dushyantyadav0303/Ruby-Home-Automation/Render/ruby-render/0003.png

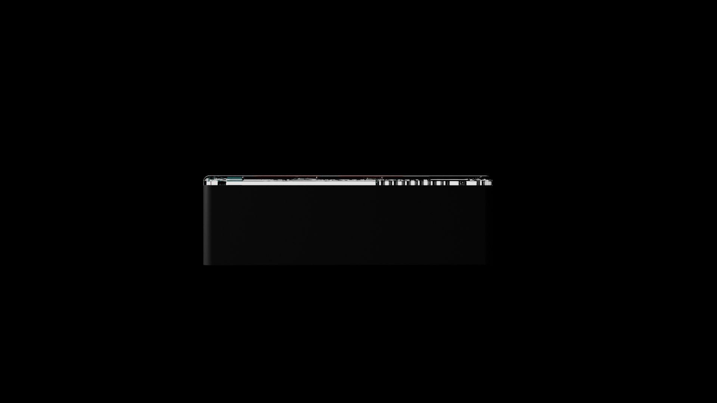
Render/ruby-render/0003.png
