dushyantyadav0303/Ruby-Home-Automation/Render/ruby-render/0030.png

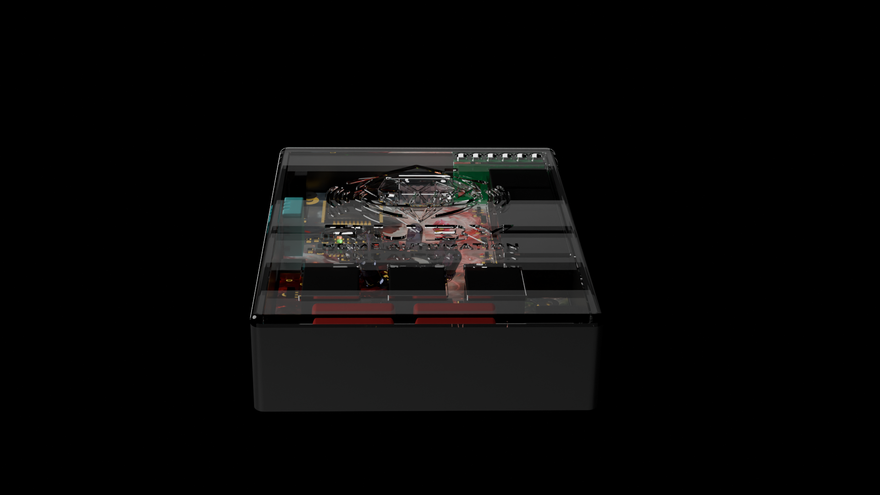
Render/ruby-render/0030.png
