dushyantyadav0303/Ruby-Home-Automation/Render/ruby-render/0039.png

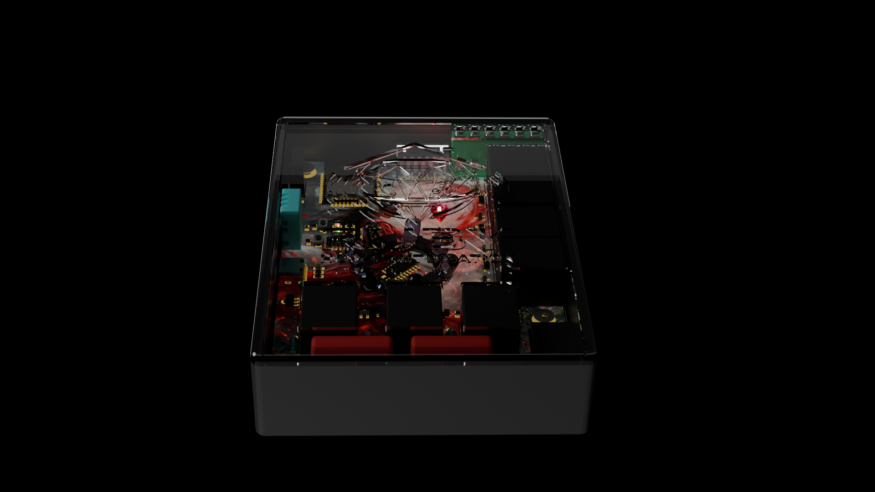
Render/ruby-render/0039.png
