dushyantyadav0303/Ruby-Home-Automation/Render/ruby-render/0087.png

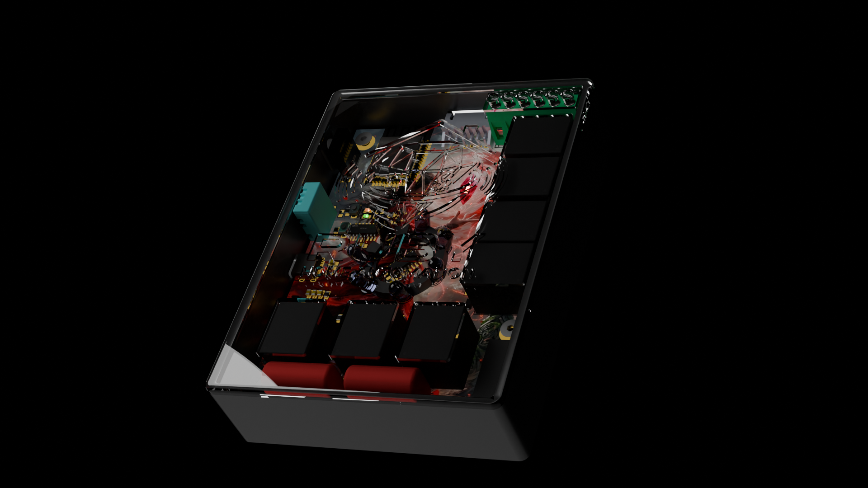
Render/ruby-render/0087.png
