dushyantyadav0303/Ruby-Home-Automation/Render/ruby-render/0092.png

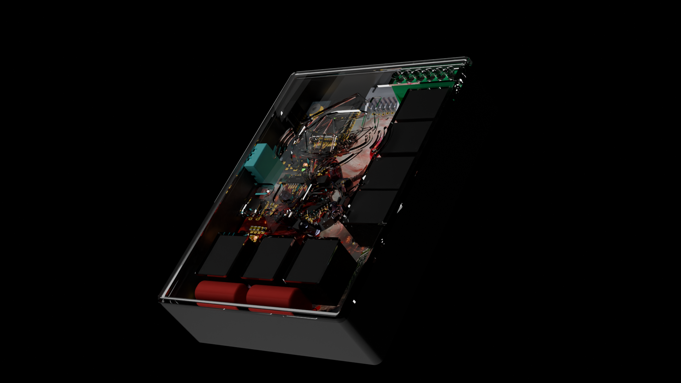
Render/ruby-render/0092.png
