dushyantyadav0303/Ruby-Home-Automation/Render/ruby-render/0105.png

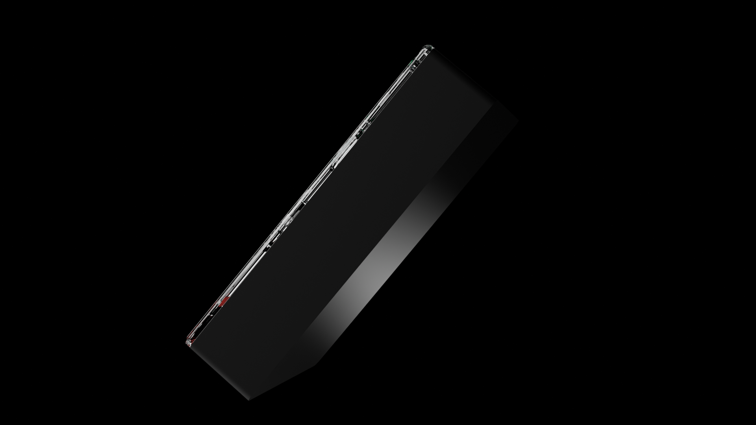
Render/ruby-render/0105.png
