dushyantyadav0303/Ruby-Home-Automation/Render/ruby-render/0107.png

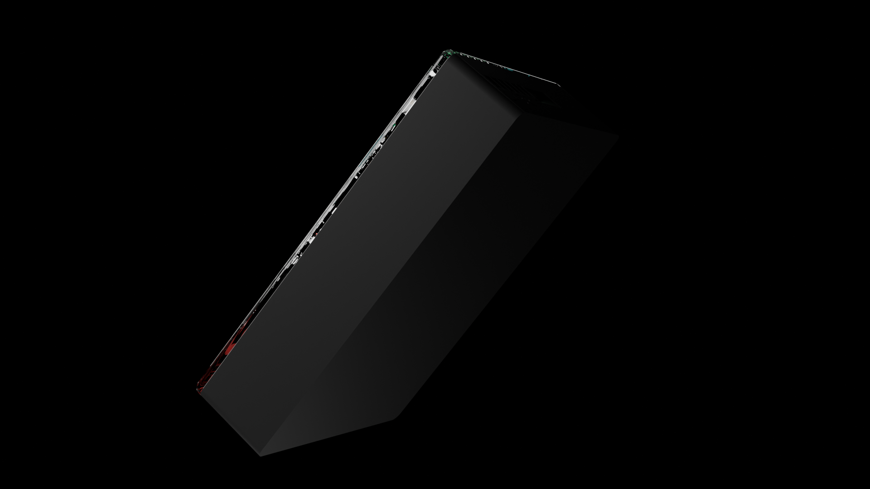
Render/ruby-render/0107.png
