dushyantyadav0303/Ruby-Home-Automation/Render/ruby-render/0113.png

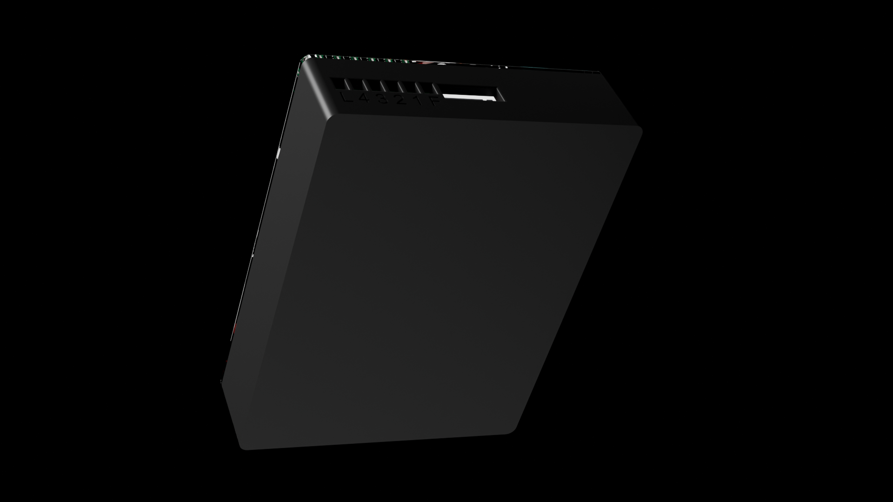
Render/ruby-render/0113.png
