dushyantyadav0303/Ruby-Home-Automation/Render/ruby-render/0117.png

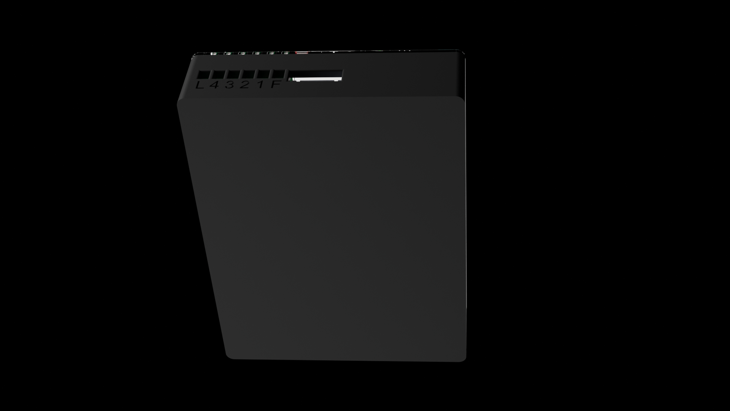
Render/ruby-render/0117.png
