dushyantyadav0303/Ruby-Home-Automation/Render/ruby-render/0119.png

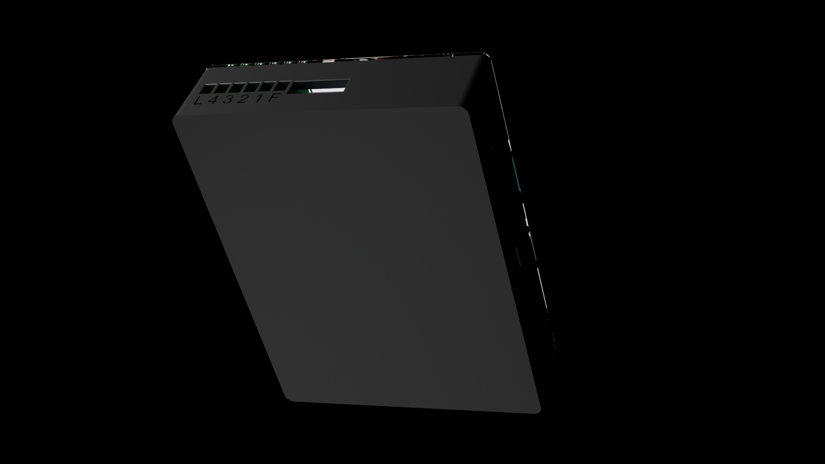
Render/ruby-render/0119.png
