dushyantyadav0303/Ruby-Home-Automation/Render/ruby-render/0123.png

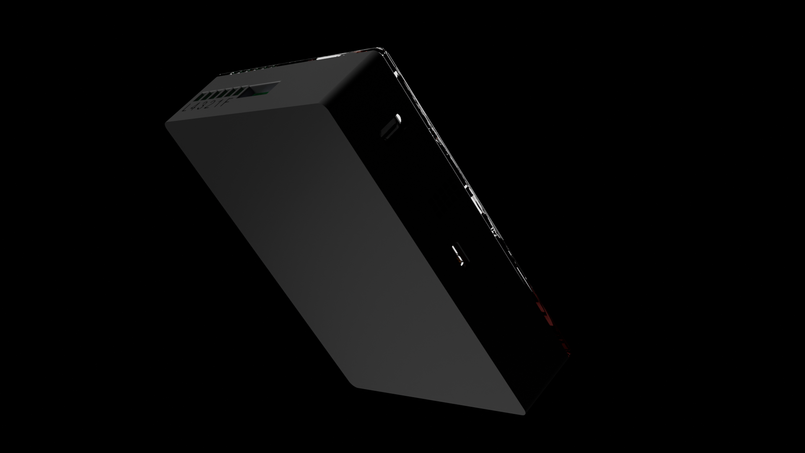
Render/ruby-render/0123.png
