dushyantyadav0303/Ruby-Home-Automation/Render/ruby-render/0125.png

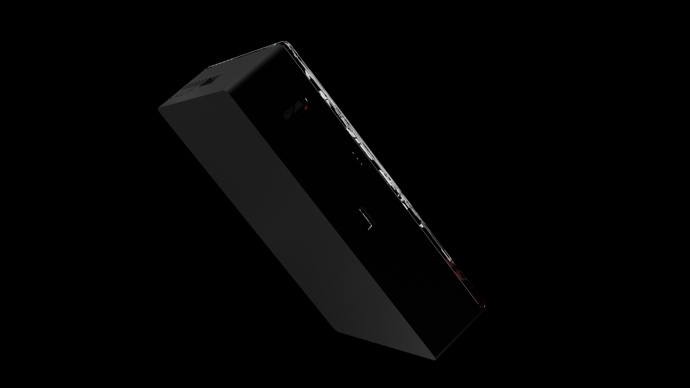
Render/ruby-render/0125.png
