dushyantyadav0303/Ruby-Home-Automation/Render/ruby-render/0128.png

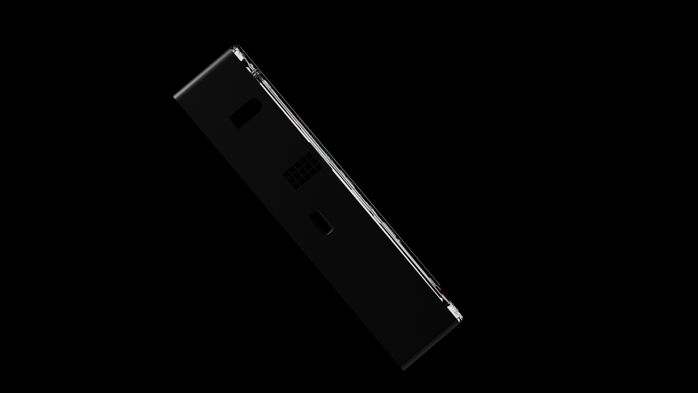
Render/ruby-render/0128.png
