dushyantyadav0303/Ruby-Home-Automation/Render/ruby-render/0132.png

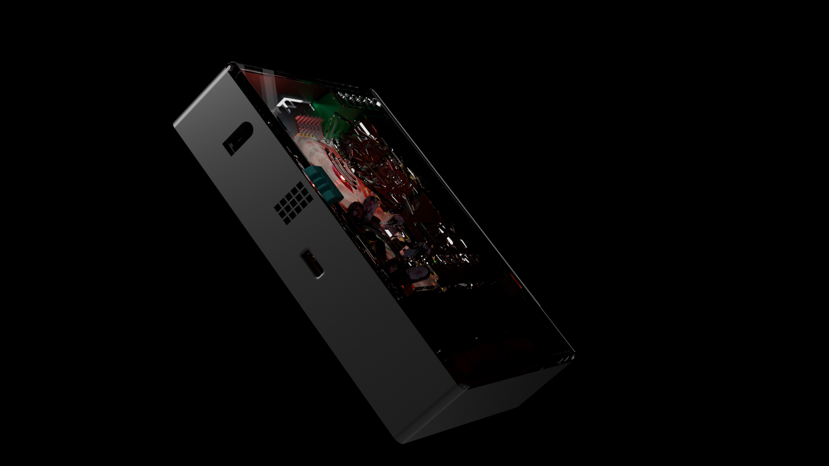
Render/ruby-render/0132.png
