dushyantyadav0303/Ruby-Home-Automation/Render/ruby-render/0135.png

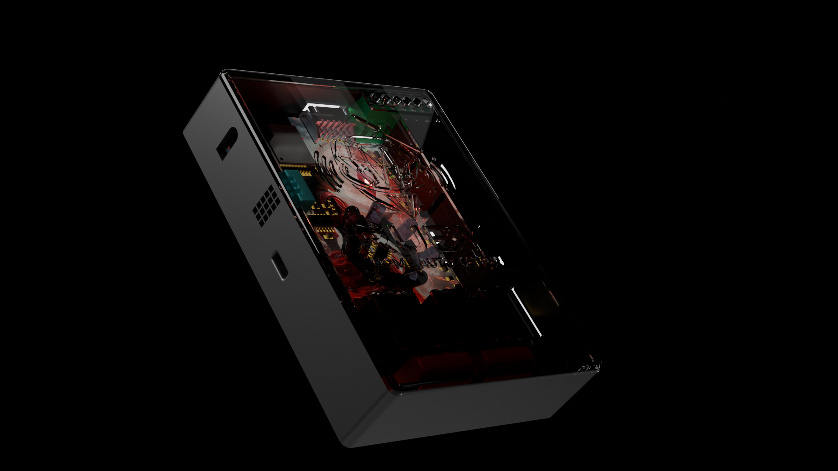
Render/ruby-render/0135.png
