dushyantyadav0303/Ruby-Home-Automation/Render/ruby-render/0141.png

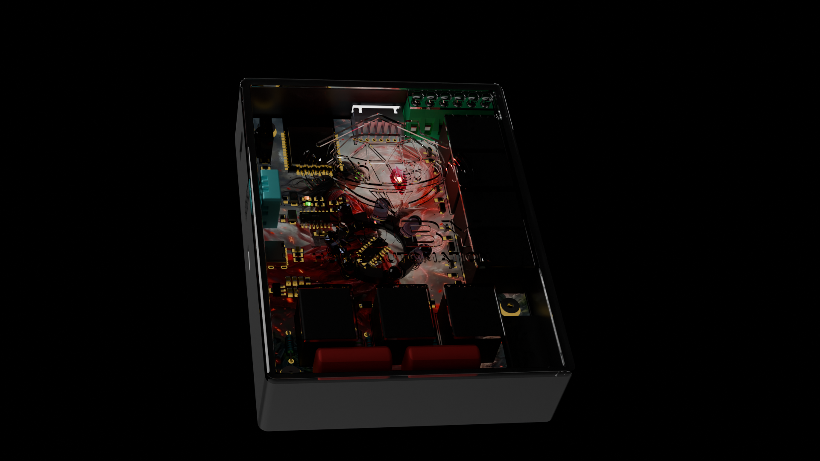
Render/ruby-render/0141.png
