dushyantyadav0303/Ruby-Home-Automation/Render/ruby-render/0150.png

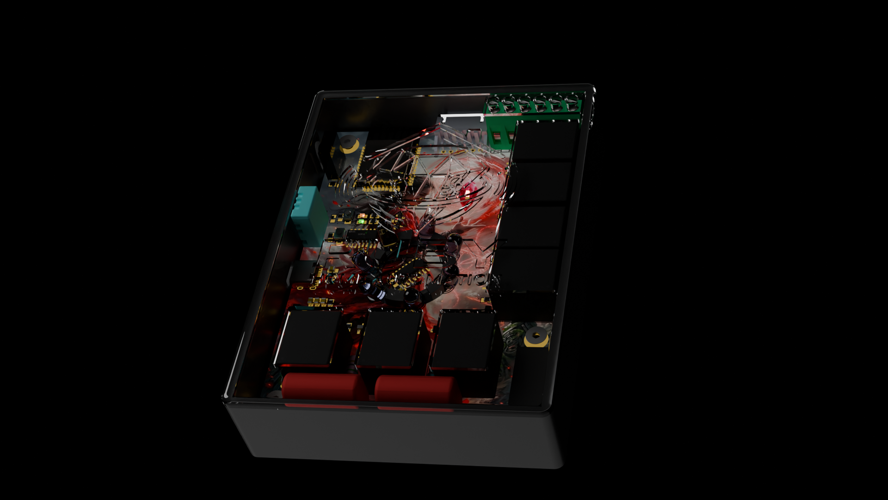
Render/ruby-render/0150.png
