dushyantyadav0303/Ruby-Home-Automation/Render/ruby-render/0172.png

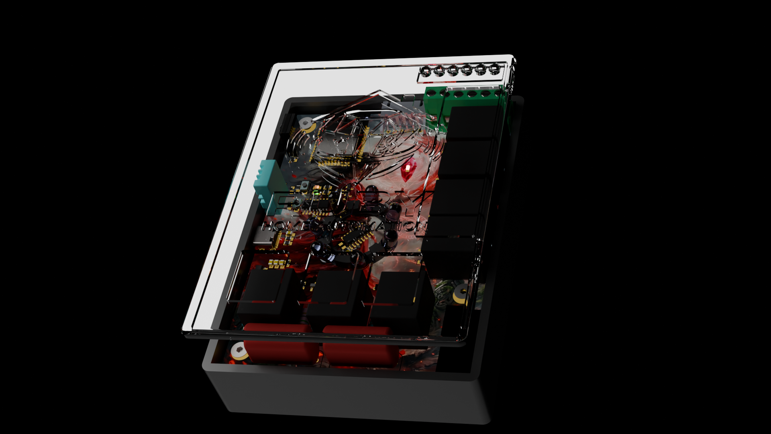
Render/ruby-render/0172.png
