dushyantyadav0303/Ruby-Home-Automation/Render/ruby-render/0174.png

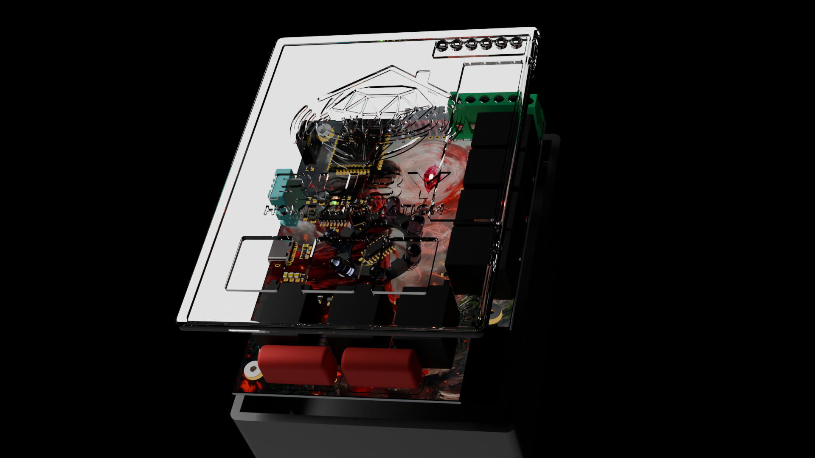
Render/ruby-render/0174.png
