dushyantyadav0303/Ruby-Home-Automation/Render/ruby-render/0175.png

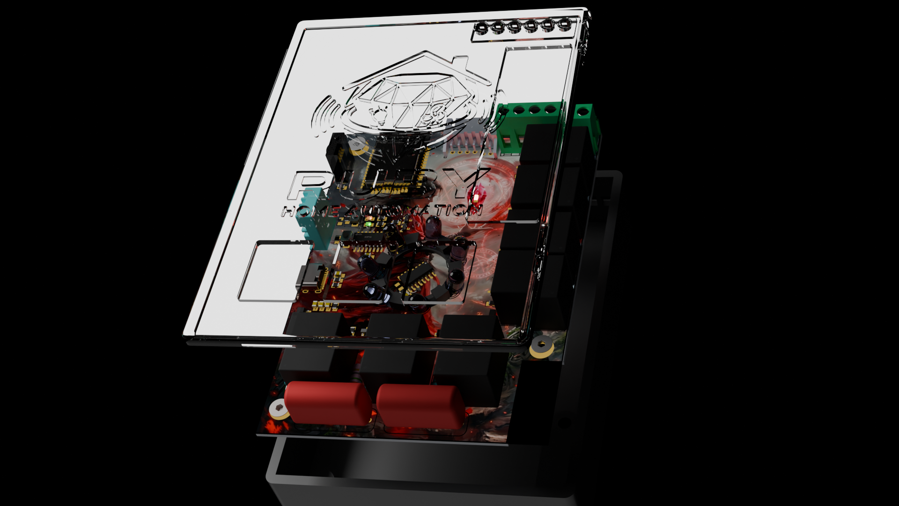
Render/ruby-render/0175.png
