dushyantyadav0303/Ruby-Home-Automation/Render/ruby-render/0176.png

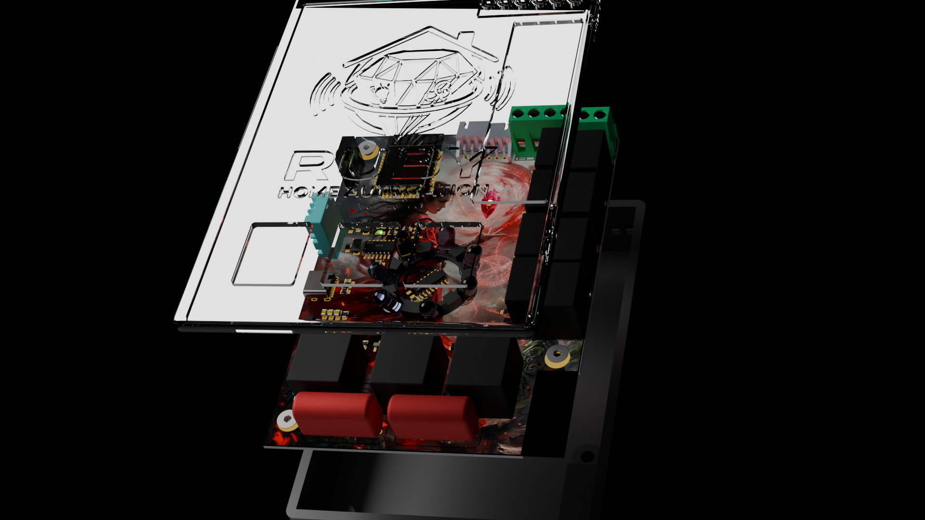
Render/ruby-render/0176.png
