dushyantyadav0303/Ruby-Home-Automation/Render/ruby-render/0179.png

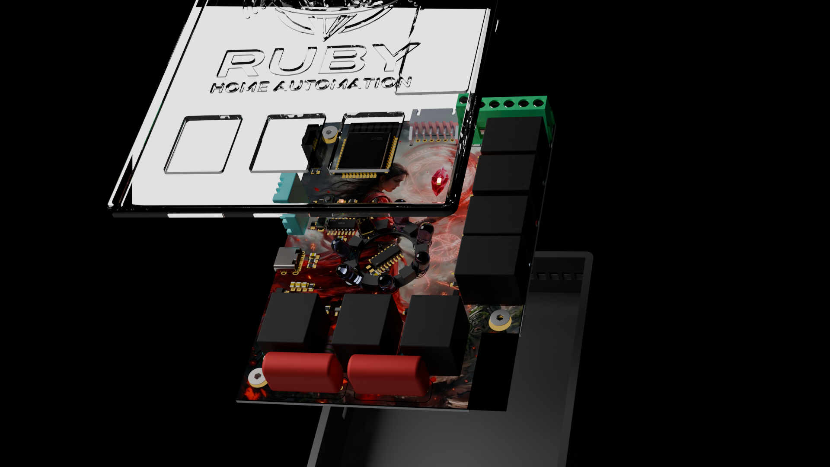
Render/ruby-render/0179.png
