dushyantyadav0303/Ruby-Home-Automation/Render/ruby-render/0182.png

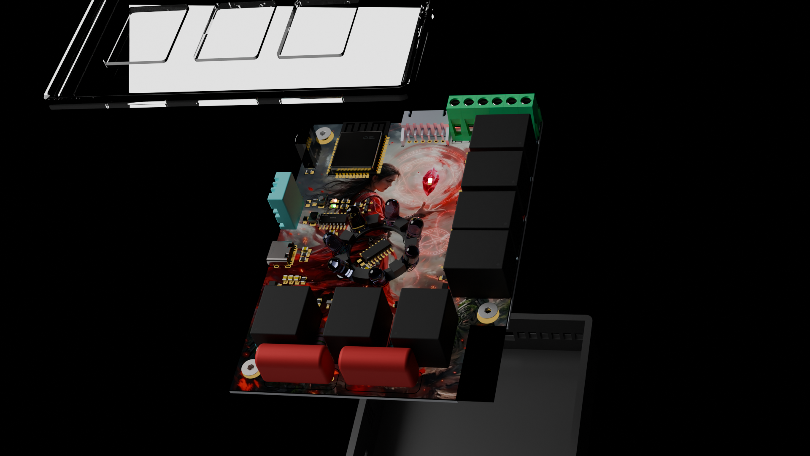
Render/ruby-render/0182.png
