dushyantyadav0303/Ruby-Home-Automation/Render/ruby-render/0186.png

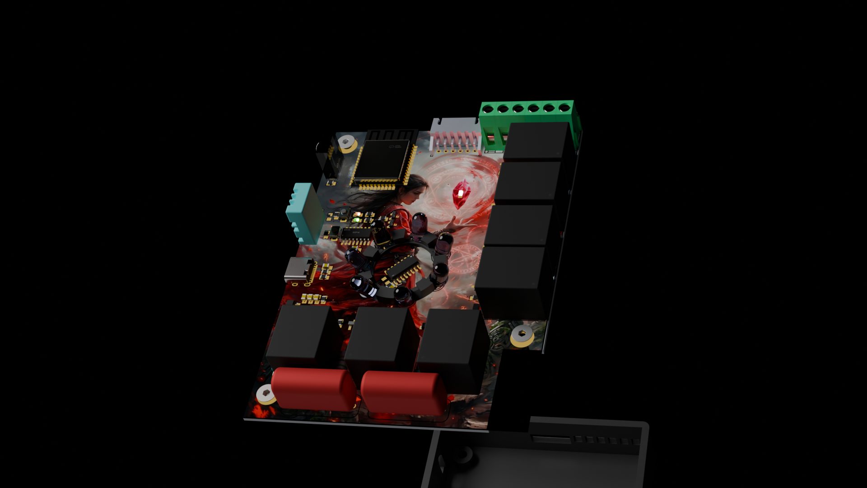
Render/ruby-render/0186.png
