dushyantyadav0303/Ruby-Home-Automation/Render/ruby-render/0207.png

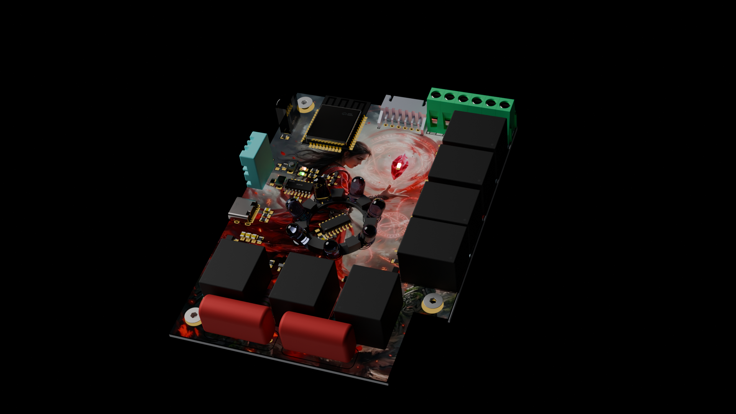
Render/ruby-render/0207.png
