dushyantyadav0303/Ruby-Home-Automation/Render/ruby-render/0215.png

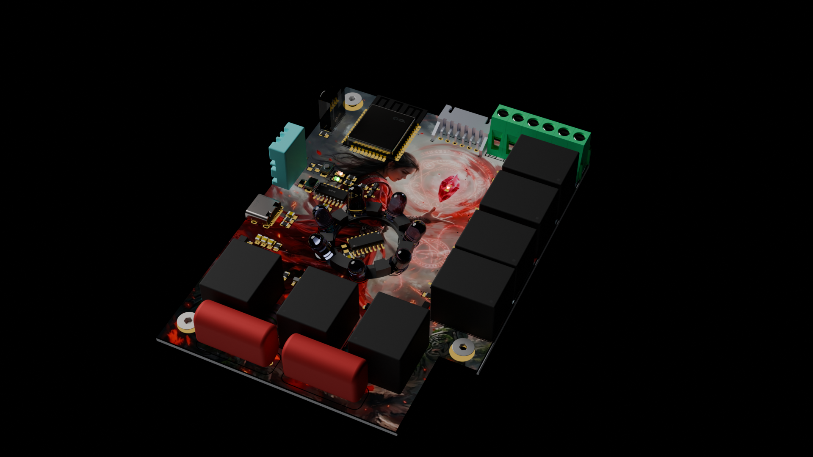
Render/ruby-render/0215.png
