dushyantyadav0303/Ruby-Home-Automation/Render/ruby-render/0223.png

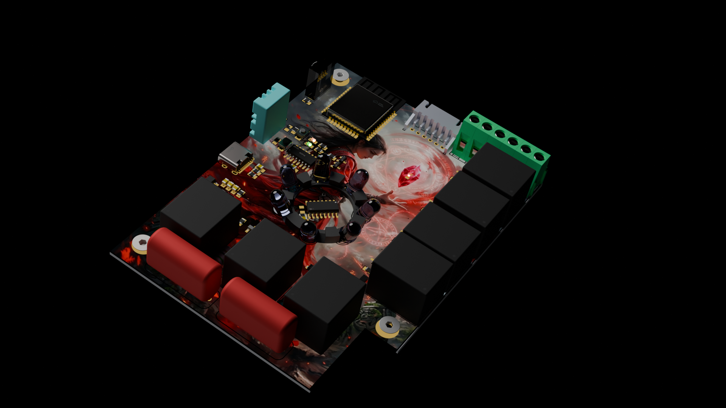
Render/ruby-render/0223.png
