dushyantyadav0303/Ruby-Home-Automation/Render/ruby-render/0230.png

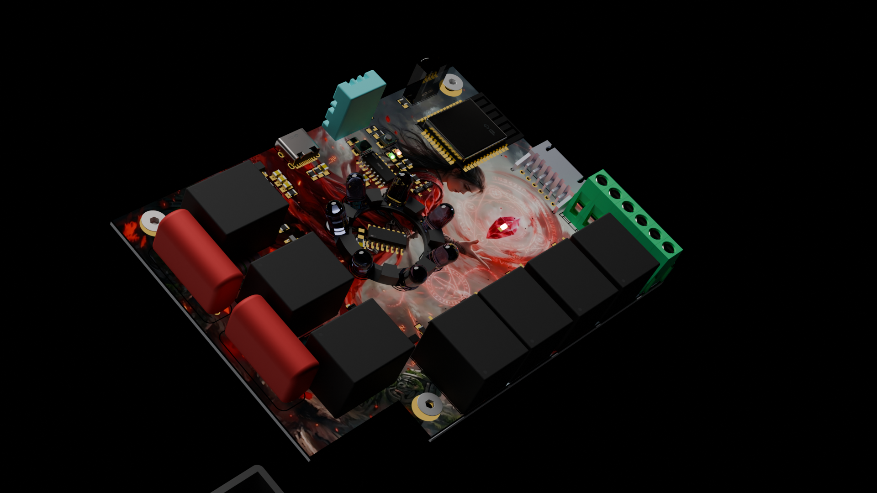
Render/ruby-render/0230.png
