dushyantyadav0303/Ruby-Home-Automation/Render/ruby-render/0233.png

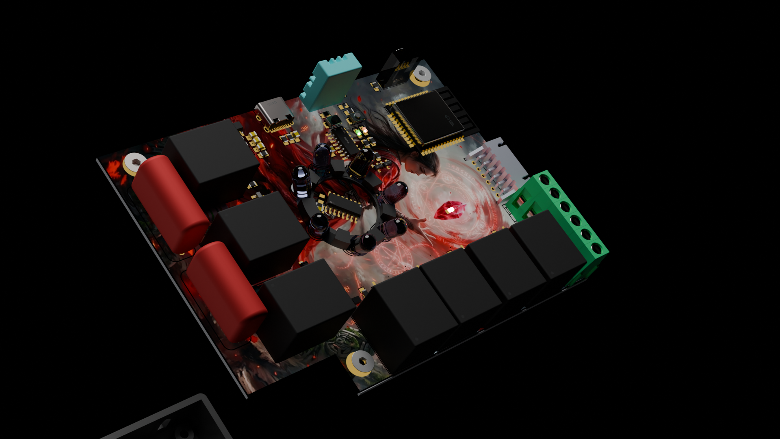
Render/ruby-render/0233.png
