dushyantyadav0303/Ruby-Home-Automation/Render/ruby-render/0237.png

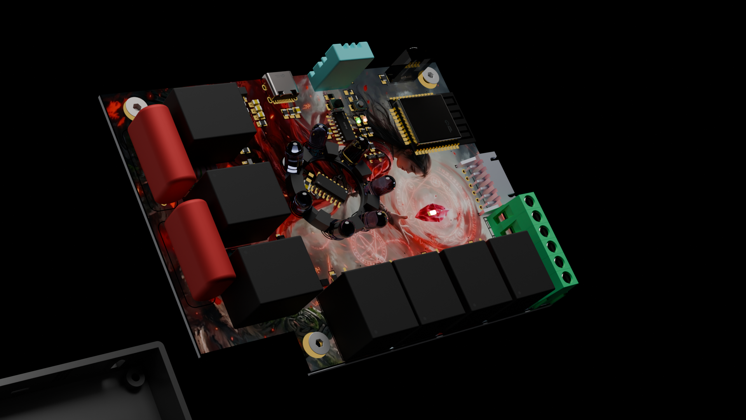
Render/ruby-render/0237.png
