dushyantyadav0303/Ruby-Home-Automation/Render/ruby-render/0243.png

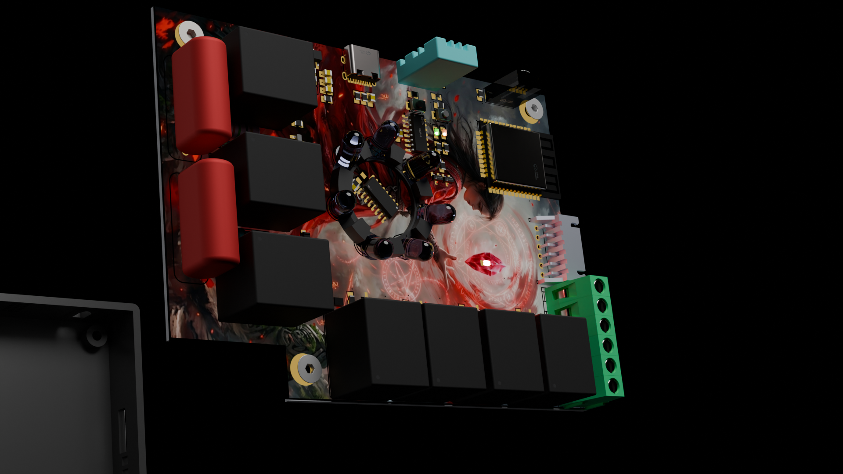
Render/ruby-render/0243.png
