dushyantyadav0303/Ruby-Home-Automation/Render/ruby-render/0248.png

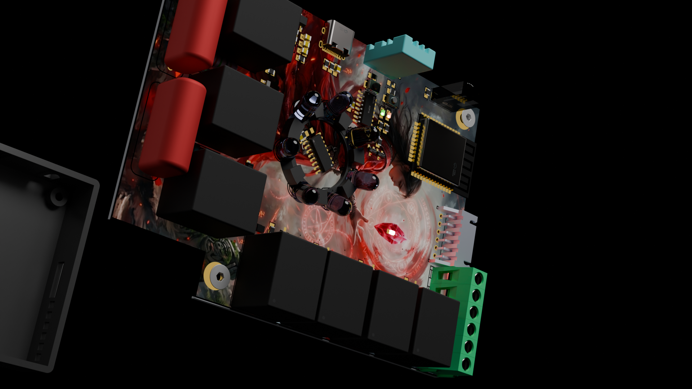
Render/ruby-render/0248.png
