dushyantyadav0303/Ruby-Home-Automation/Render/ruby-render/0249.png

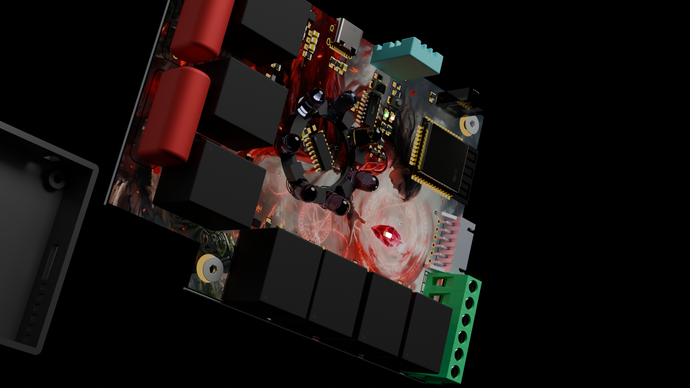
Render/ruby-render/0249.png
