dushyantyadav0303/Ruby-Home-Automation/Render/ruby-render/0250.png

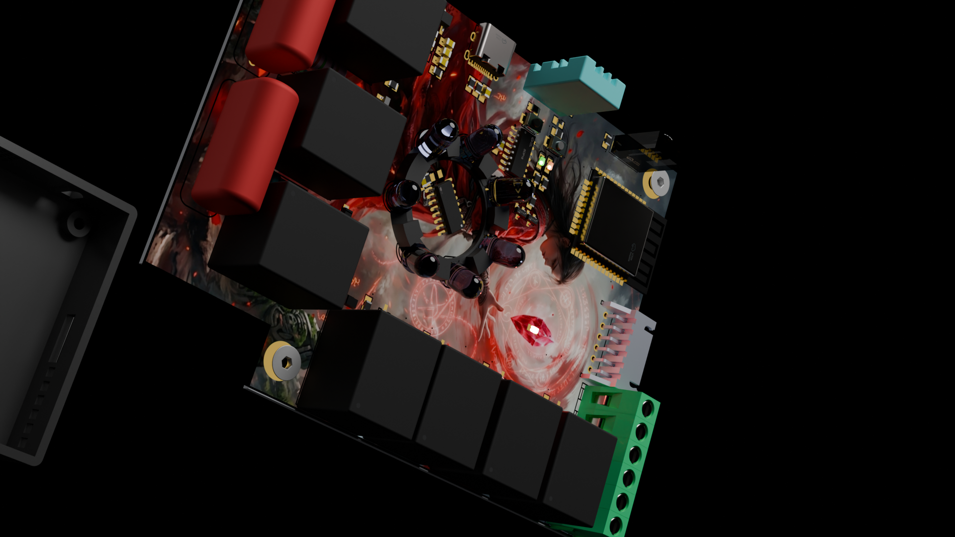
Render/ruby-render/0250.png
