dushyantyadav0303/Ruby-Home-Automation/Render/ruby-render/0254.png

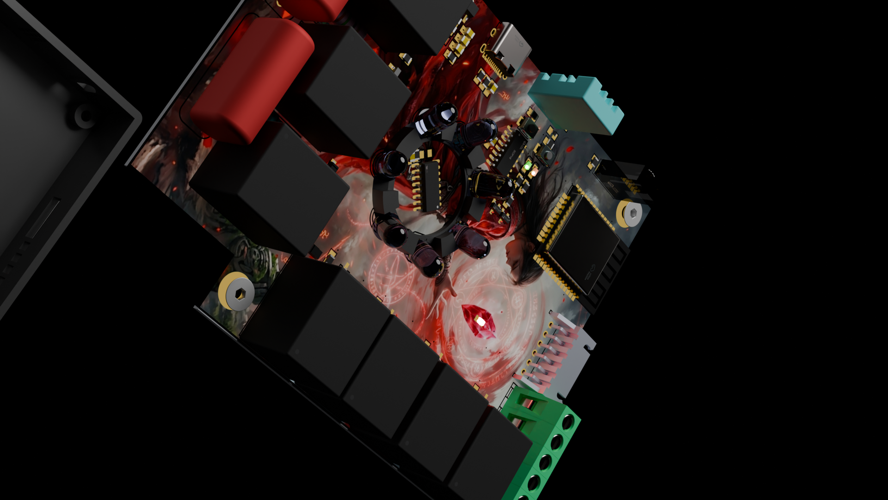
Render/ruby-render/0254.png
