dushyantyadav0303/Ruby-Home-Automation/Render/ruby-render/0257.png

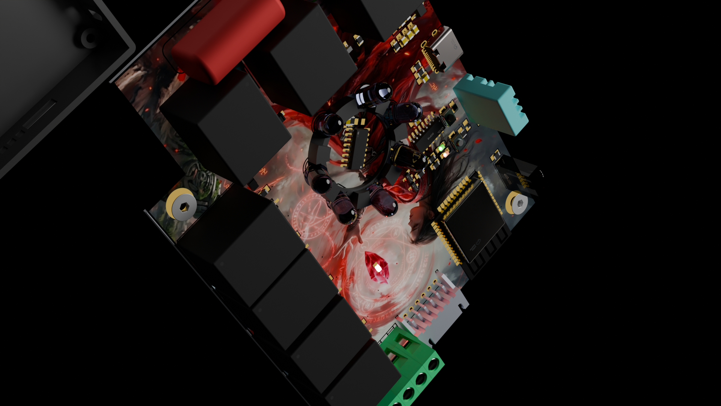
Render/ruby-render/0257.png
