dushyantyadav0303/Ruby-Home-Automation/Render/ruby-render/0259.png

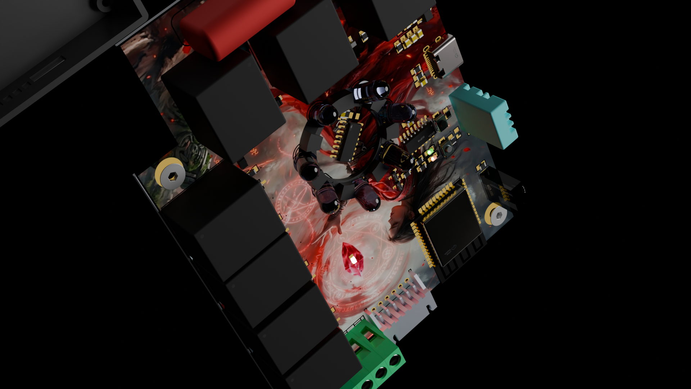
Render/ruby-render/0259.png
