dushyantyadav0303/Ruby-Home-Automation/Render/ruby-render/0264.png

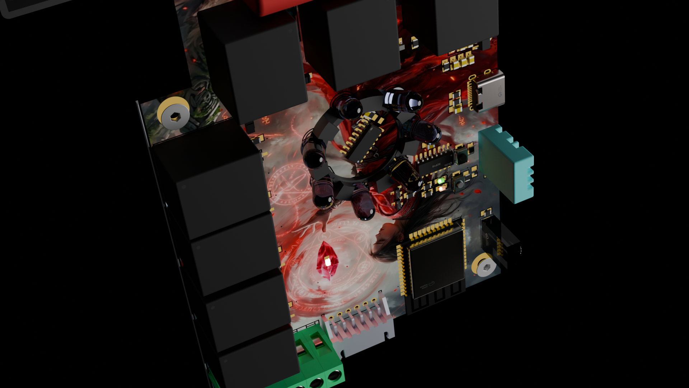
Render/ruby-render/0264.png
