dushyantyadav0303/Ruby-Home-Automation/Render/ruby-render/0266.png

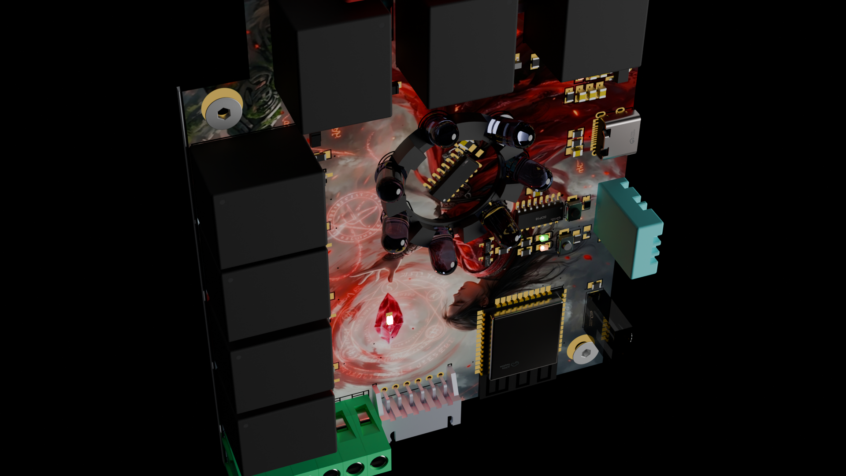
Render/ruby-render/0266.png
