dushyantyadav0303/Ruby-Home-Automation/Render/ruby-render/0268.png

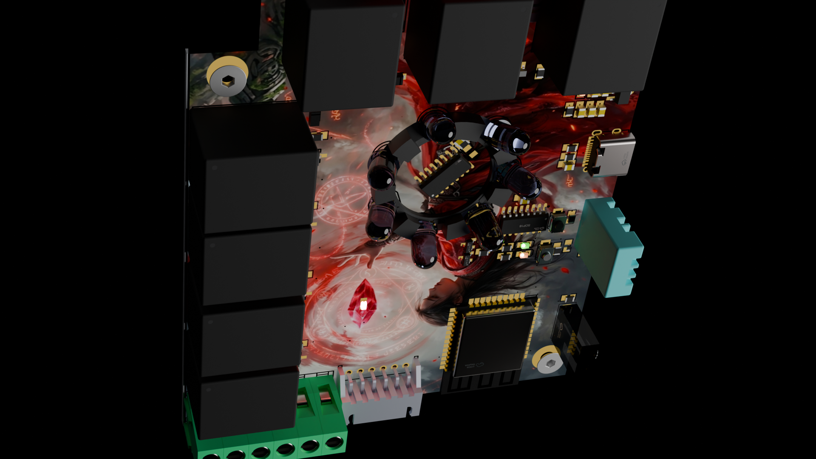
Render/ruby-render/0268.png
