dushyantyadav0303/Ruby-Home-Automation/Render/ruby-render/0279.png

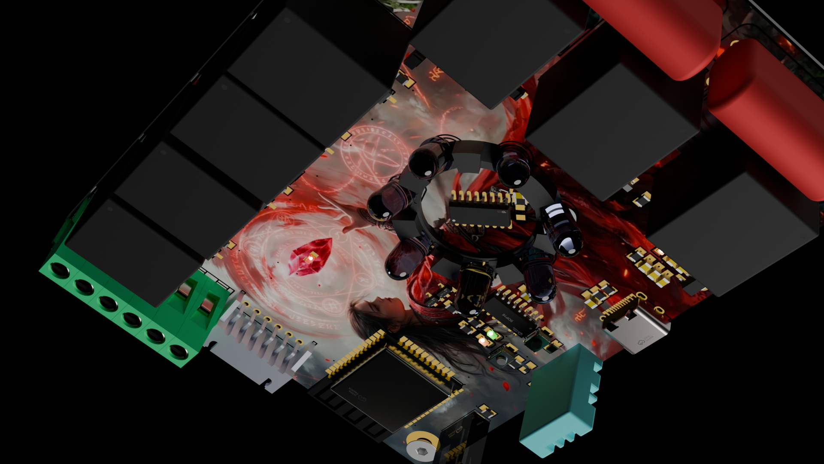
Render/ruby-render/0279.png
