dushyantyadav0303/Ruby-Home-Automation/Render/ruby-render/0280.png

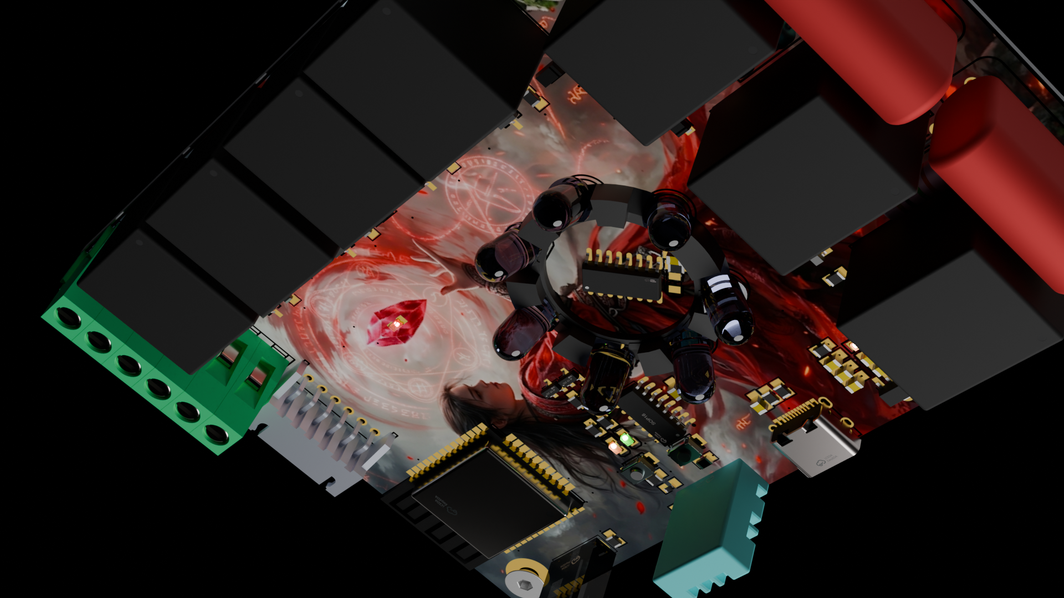
Render/ruby-render/0280.png
