dushyantyadav0303/Ruby-Home-Automation/Render/ruby-render/0281.png

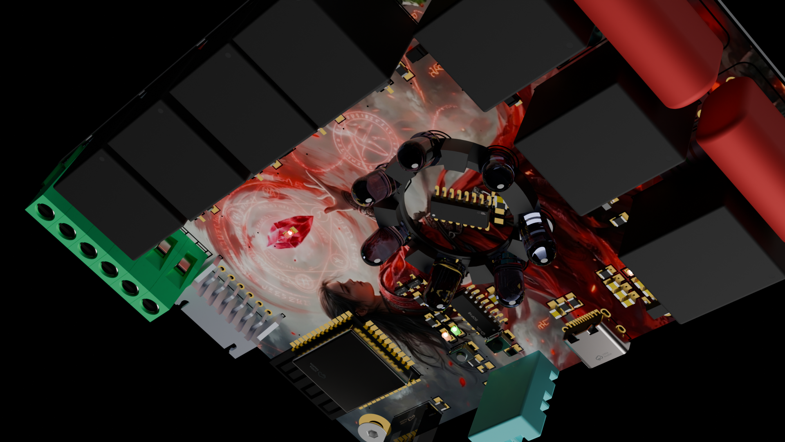
Render/ruby-render/0281.png
