dushyantyadav0303/Ruby-Home-Automation/Render/ruby-render/0284.png

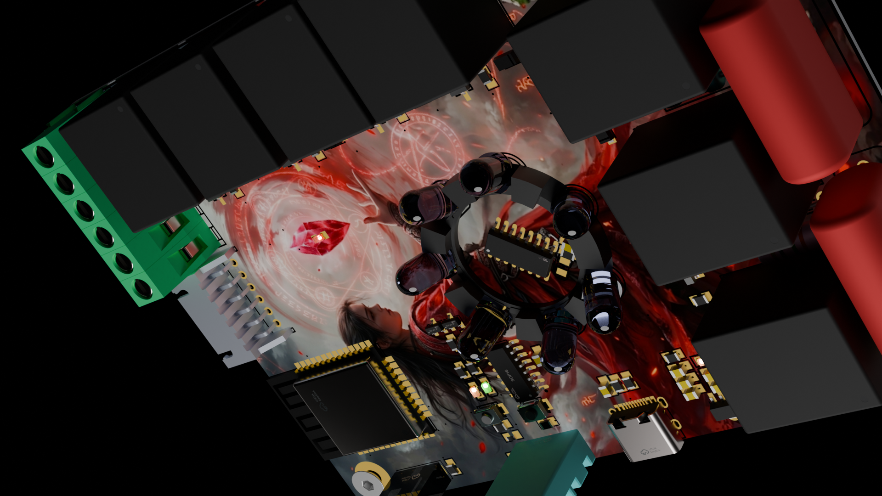
Render/ruby-render/0284.png
