dushyantyadav0303/Ruby-Home-Automation/Render/ruby-render/0285.png

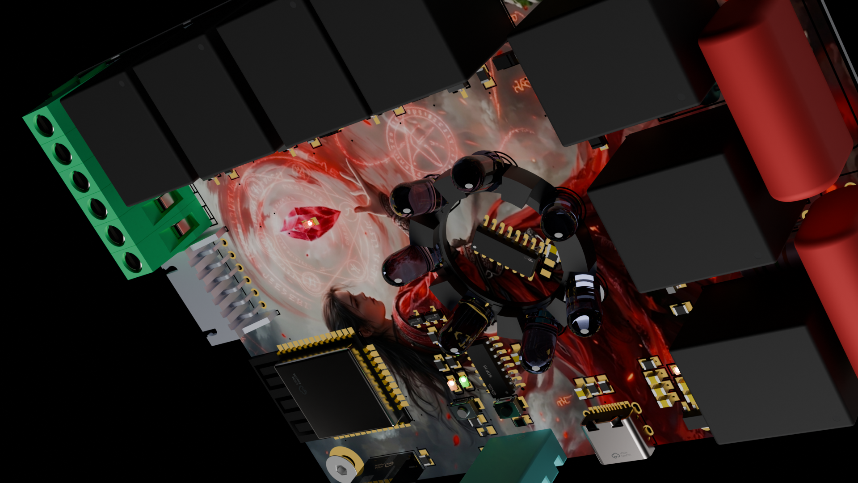
Render/ruby-render/0285.png
