dushyantyadav0303/Ruby-Home-Automation/Render/ruby-render/0288.png

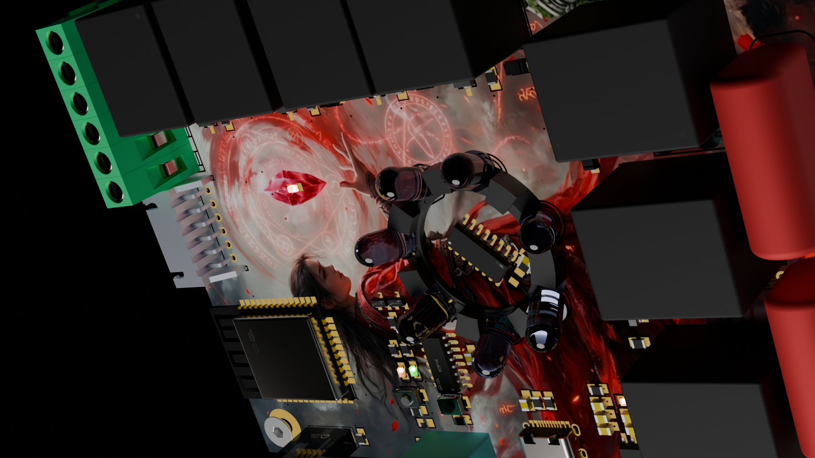
Render/ruby-render/0288.png
