dushyantyadav0303/Ruby-Home-Automation/Render/ruby-render/0289.png

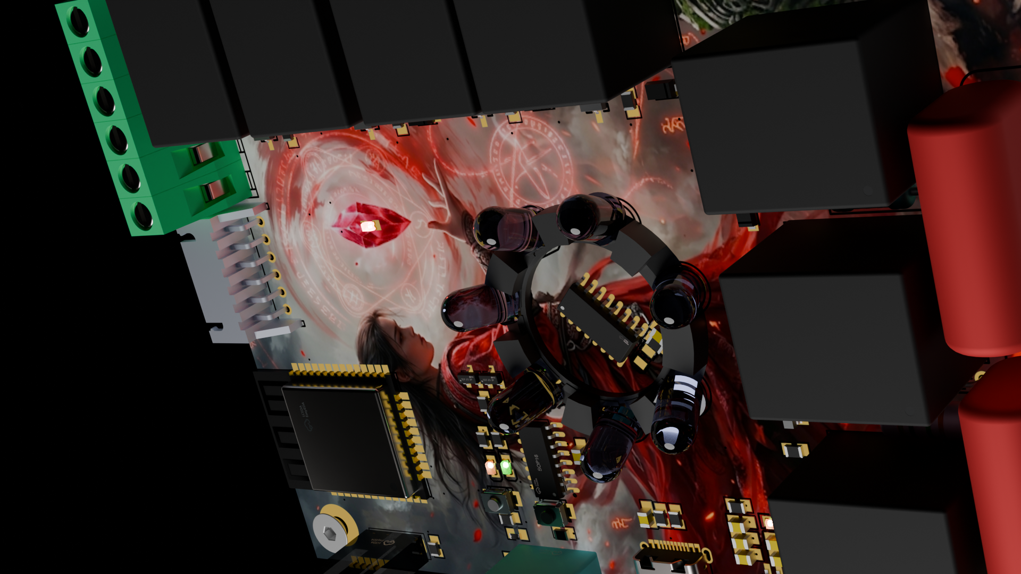
Render/ruby-render/0289.png
