dushyantyadav0303/Ruby-Home-Automation/Render/ruby-render/0290.png

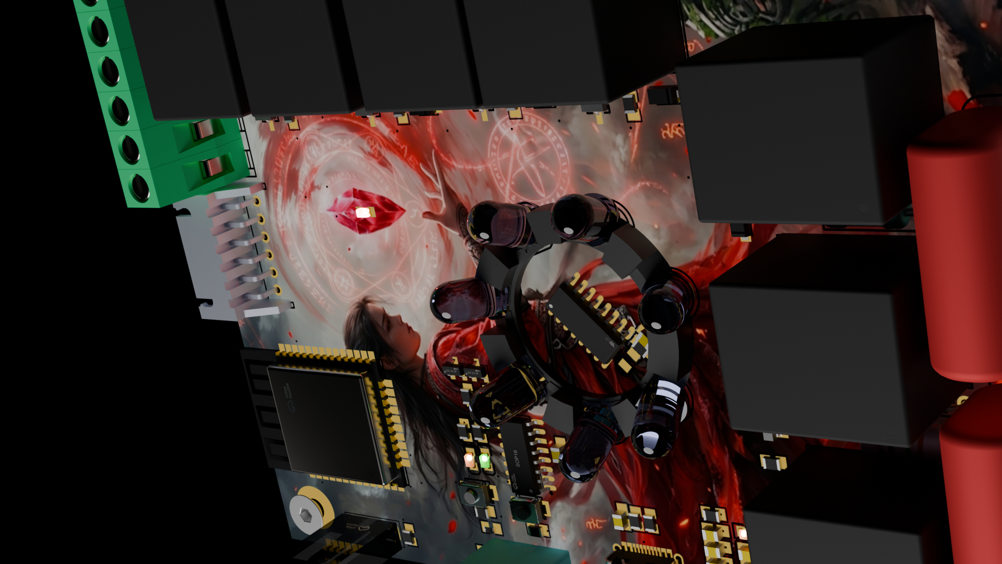
Render/ruby-render/0290.png
