dushyantyadav0303/Ruby-Home-Automation/Render/ruby-render/0291.png

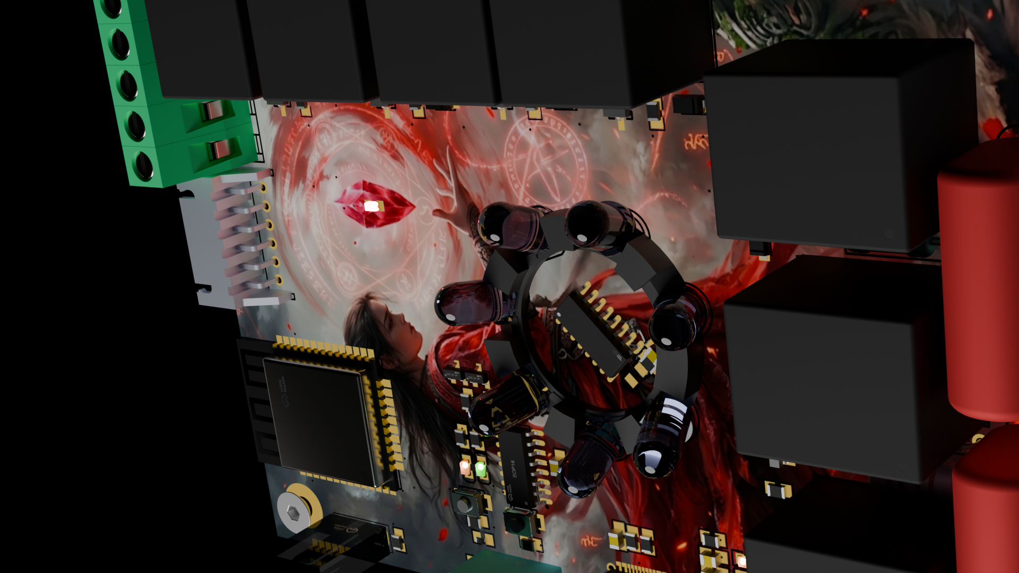
Render/ruby-render/0291.png
