dushyantyadav0303/Ruby-Home-Automation/Render/ruby-render/0292.png

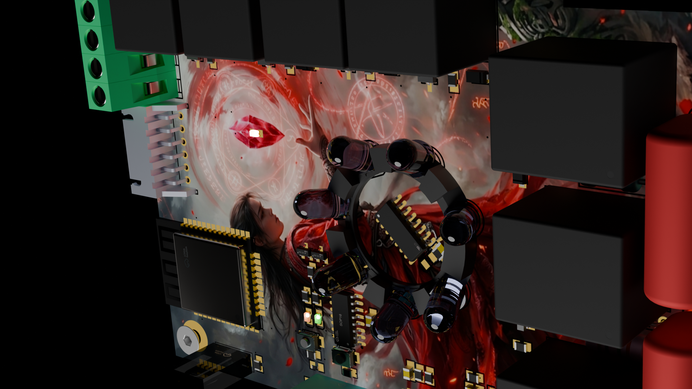
Render/ruby-render/0292.png
