dushyantyadav0303/Ruby-Home-Automation/Render/ruby-render/0294.png

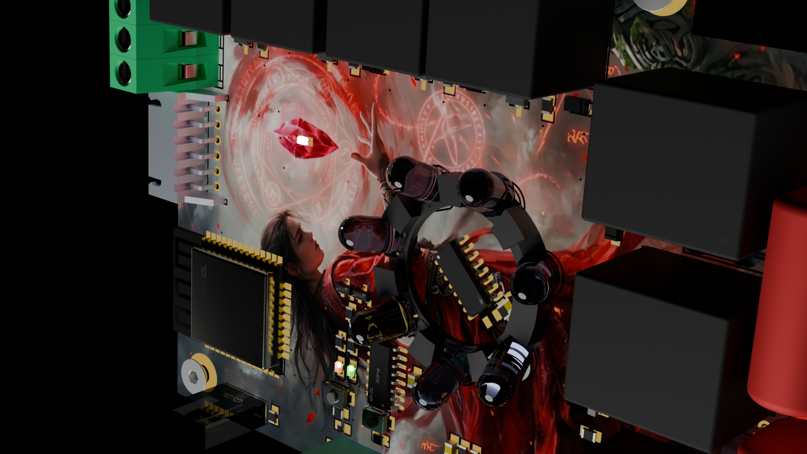
Render/ruby-render/0294.png
