dushyantyadav0303/Ruby-Home-Automation/Render/ruby-render/0304.png

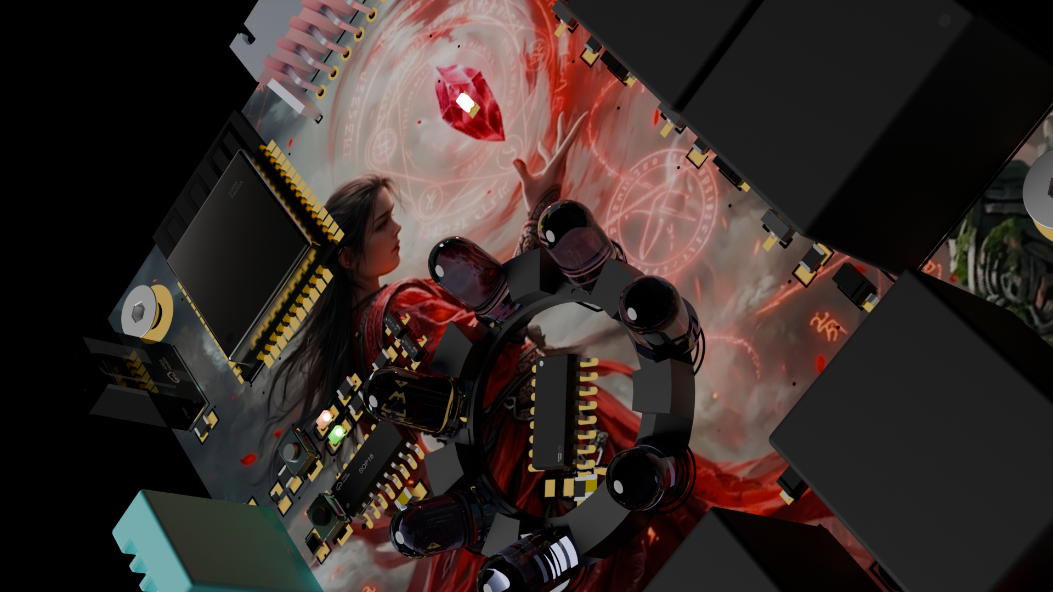
Render/ruby-render/0304.png
