dushyantyadav0303/Ruby-Home-Automation/Render/ruby-render/0305.png

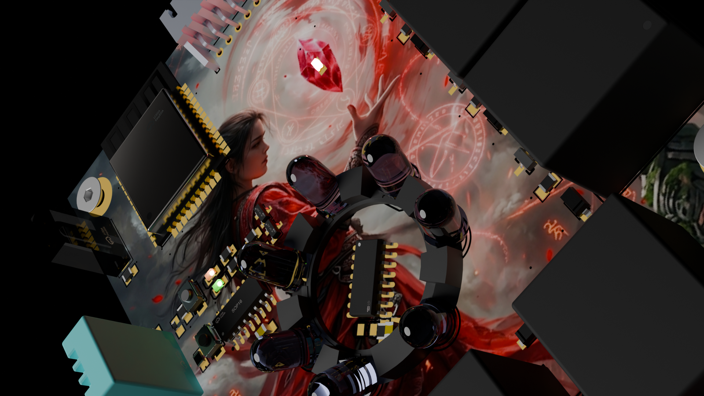
Render/ruby-render/0305.png
