dushyantyadav0303/Ruby-Home-Automation/Render/ruby-render/0309.png

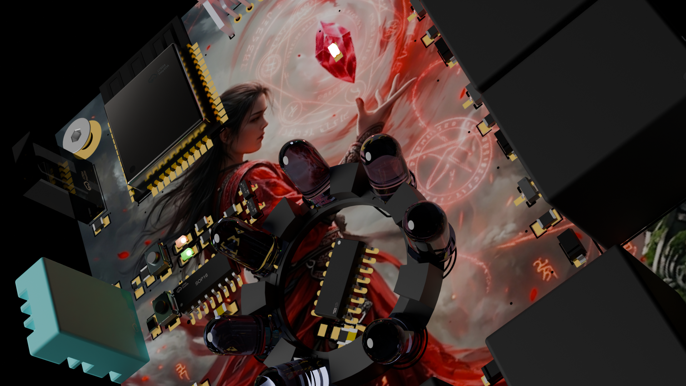
Render/ruby-render/0309.png
