dushyantyadav0303/Ruby-Home-Automation/Render/ruby-render/0311.png

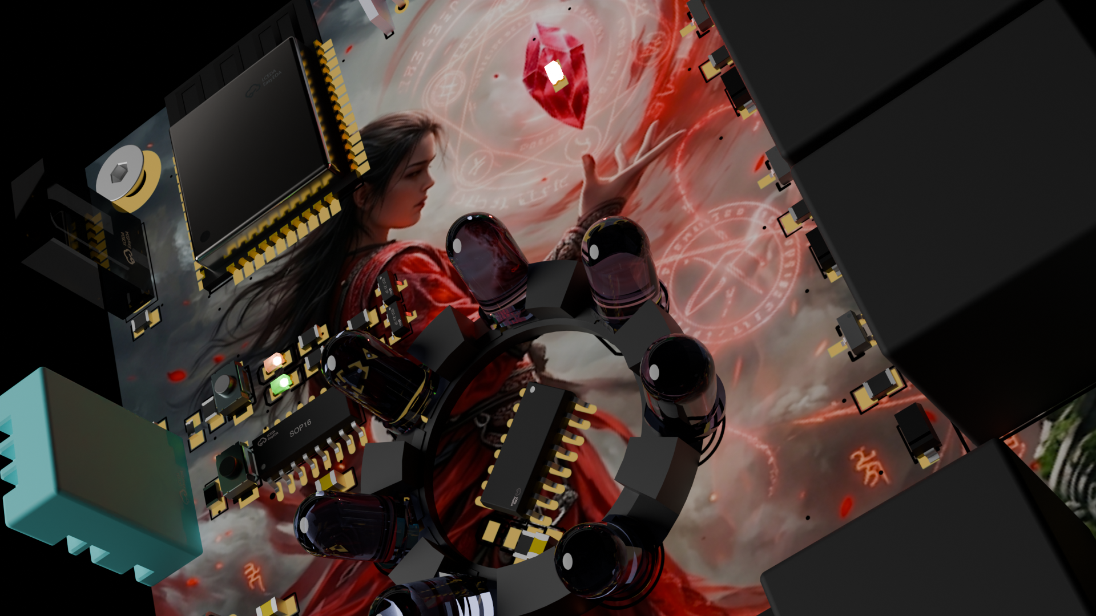
Render/ruby-render/0311.png
