dushyantyadav0303/Ruby-Home-Automation/Render/ruby-render/0312.png

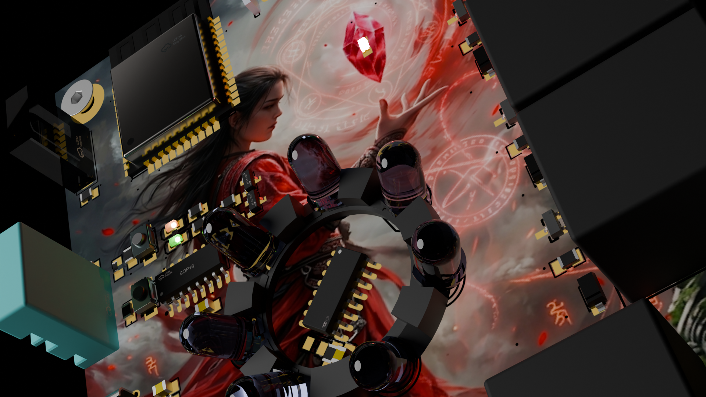
Render/ruby-render/0312.png
