dushyantyadav0303/Ruby-Home-Automation/Render/ruby-render/0316.png

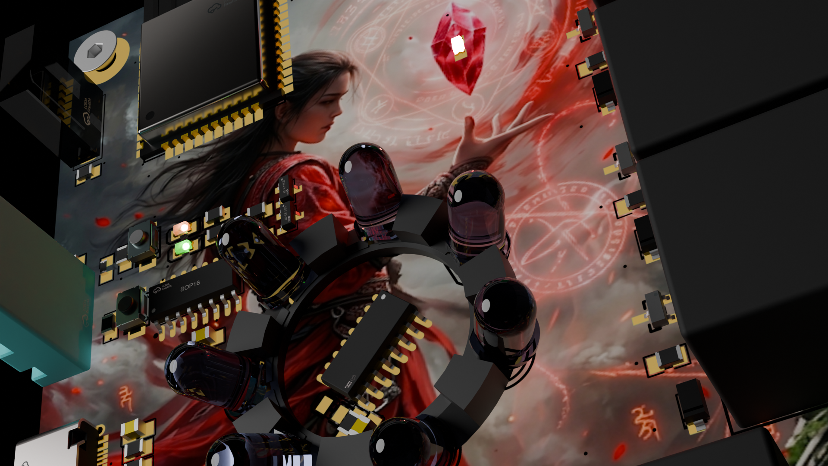
Render/ruby-render/0316.png
