dushyantyadav0303/Ruby-Home-Automation/Render/ruby-render/0319.png

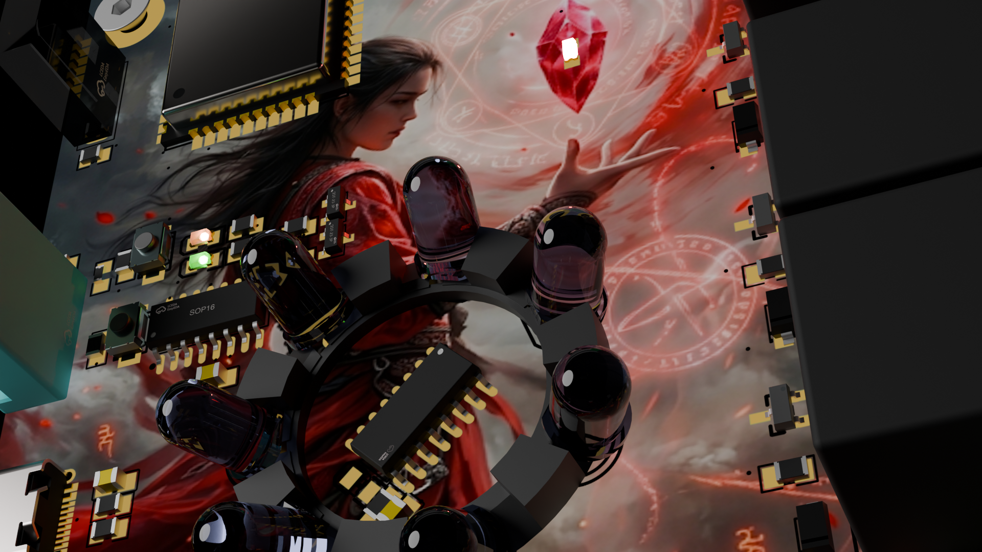
Render/ruby-render/0319.png
