dushyantyadav0303/Ruby-Home-Automation/Render/ruby-render/0322.png

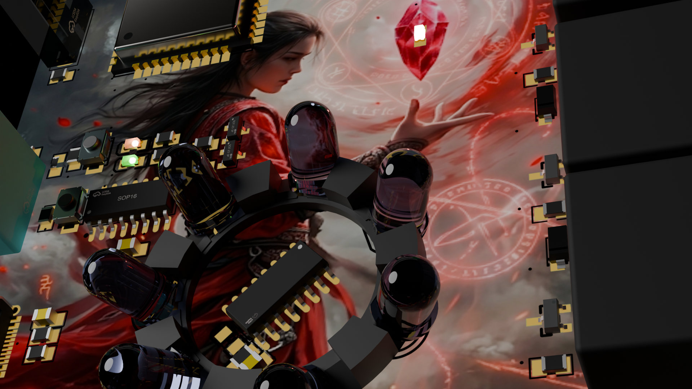
Render/ruby-render/0322.png
