dushyantyadav0303/Ruby-Home-Automation/Render/ruby-render/0327.png

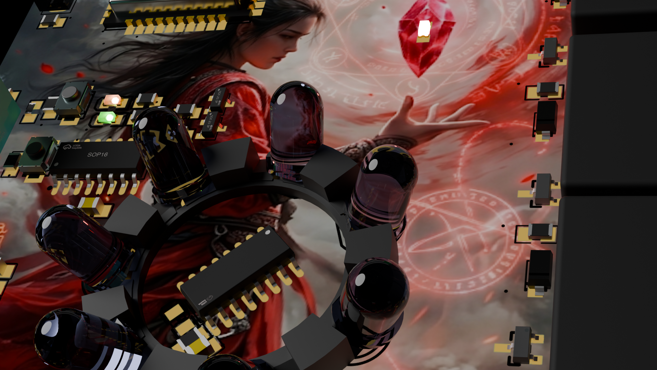
Render/ruby-render/0327.png
