dushyantyadav0303/Ruby-Home-Automation/Render/ruby-render/0332.png

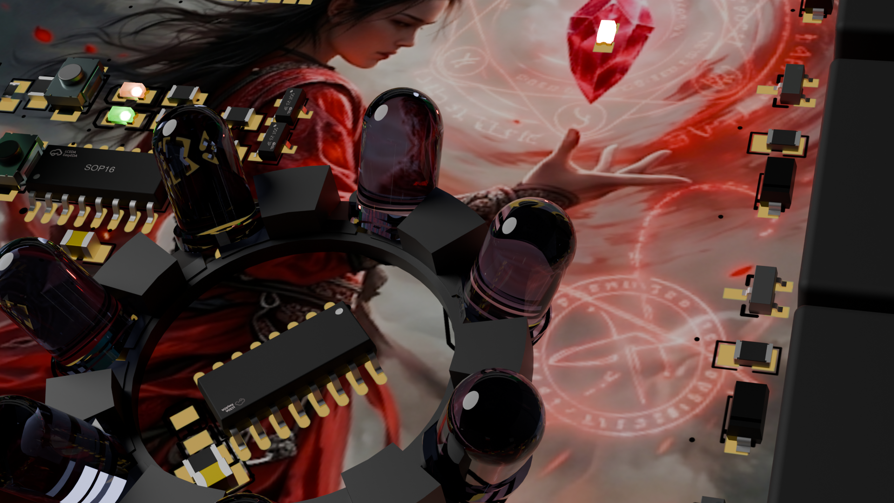
Render/ruby-render/0332.png
