dushyantyadav0303/Ruby-Home-Automation/Render/ruby-render/0333.png

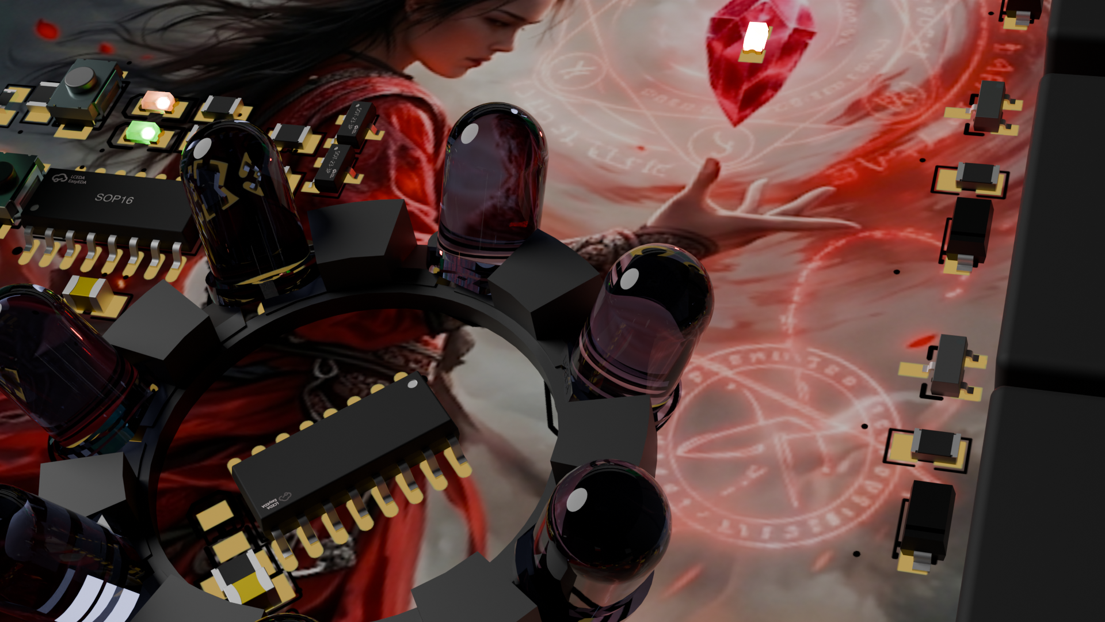
Render/ruby-render/0333.png
