dushyantyadav0303/Ruby-Home-Automation/Render/ruby-render/0337.png

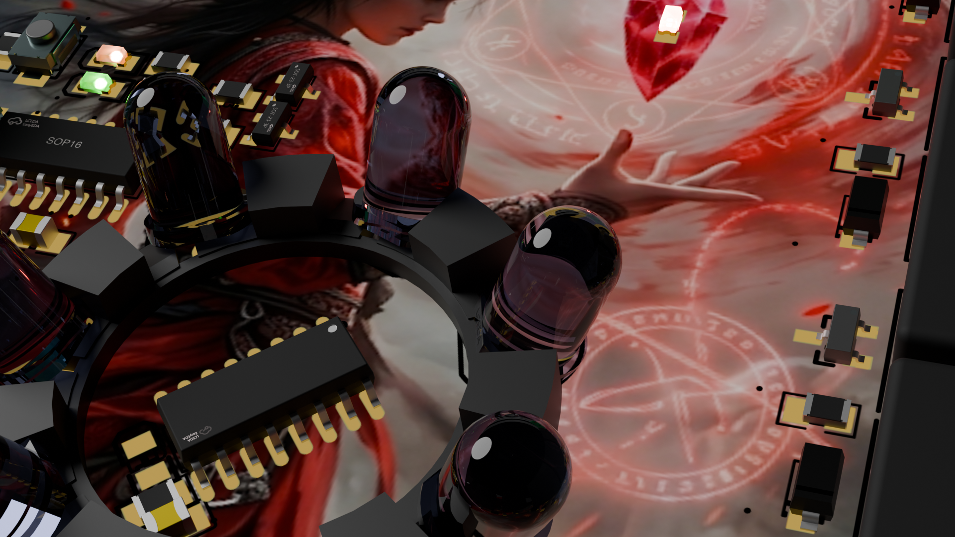
Render/ruby-render/0337.png
