dushyantyadav0303/Ruby-Home-Automation/Render/ruby-render/0342.png

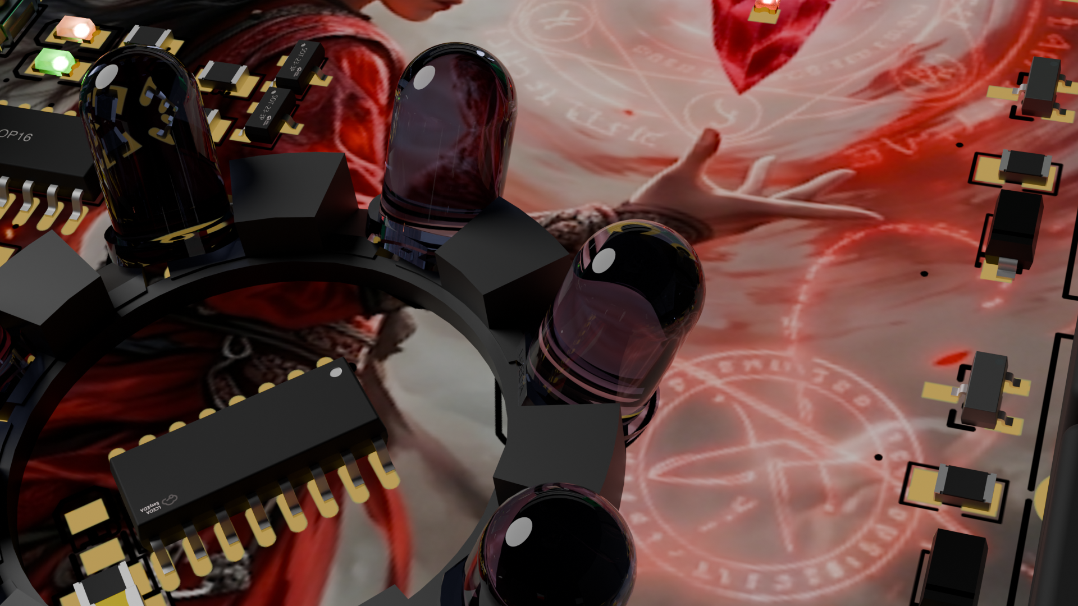
Render/ruby-render/0342.png
