dushyantyadav0303/Ruby-Home-Automation/Render/ruby-render/0347.png

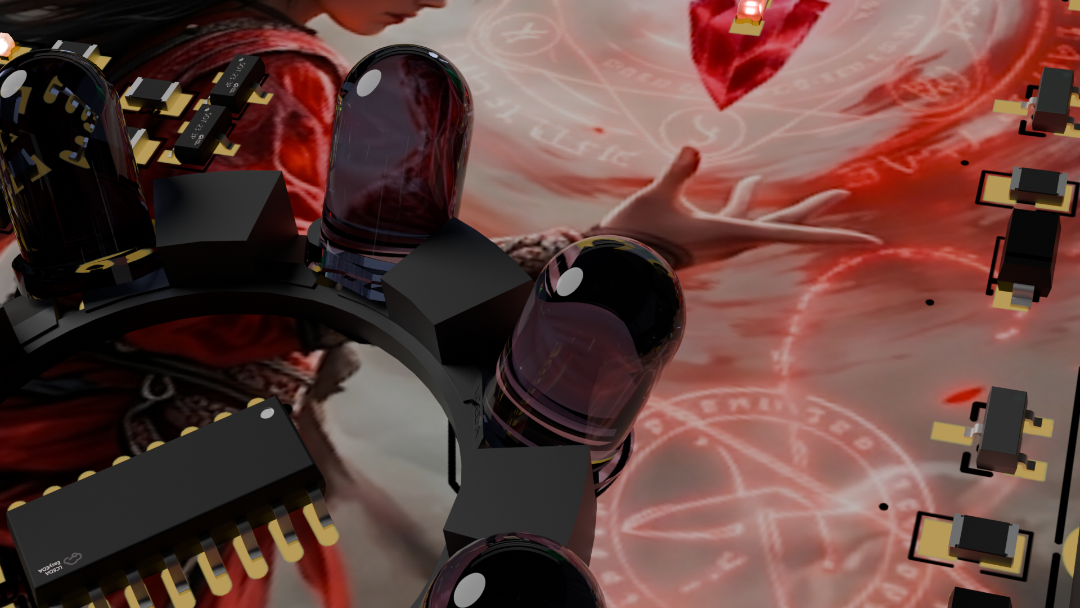
Render/ruby-render/0347.png
