dushyantyadav0303/Ruby-Home-Automation/Render/ruby-render/0352.png

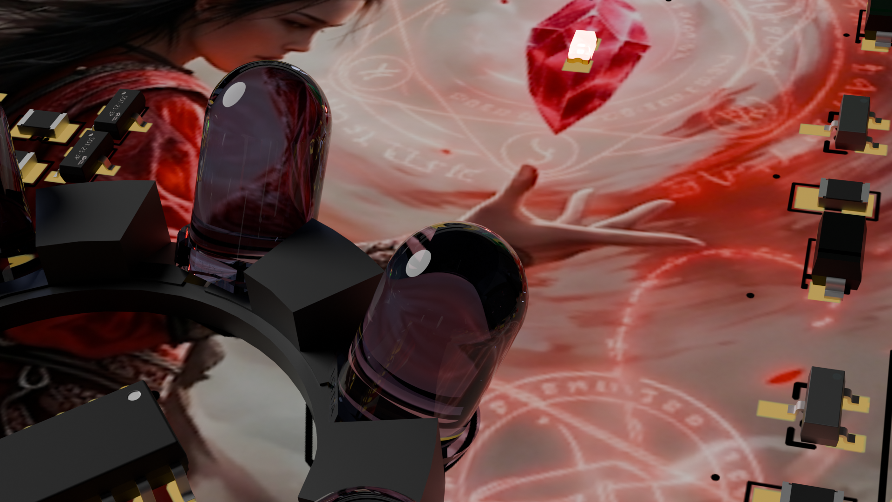
Render/ruby-render/0352.png
