dushyantyadav0303/Ruby-Home-Automation/Render/ruby-render/0355.png

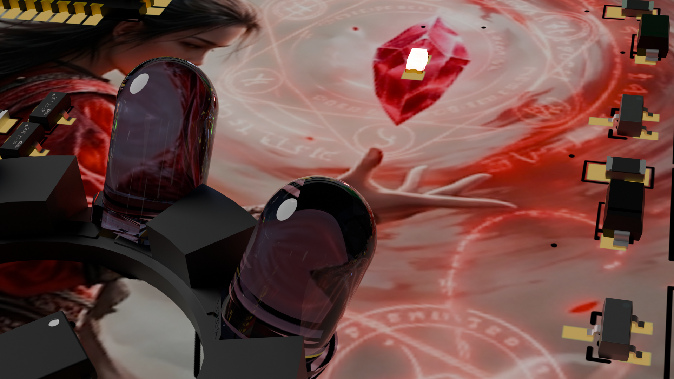
Render/ruby-render/0355.png
