dushyantyadav0303/Ruby-Home-Automation/Render/ruby-render/0358.png

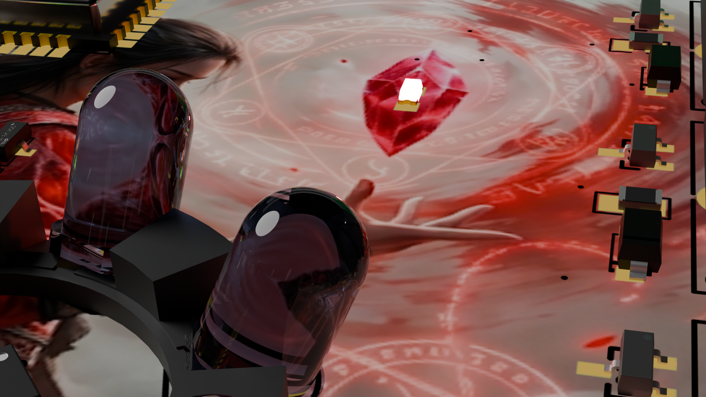
Render/ruby-render/0358.png
