dushyantyadav0303/Ruby-Home-Automation/Render/ruby-render/0360.png

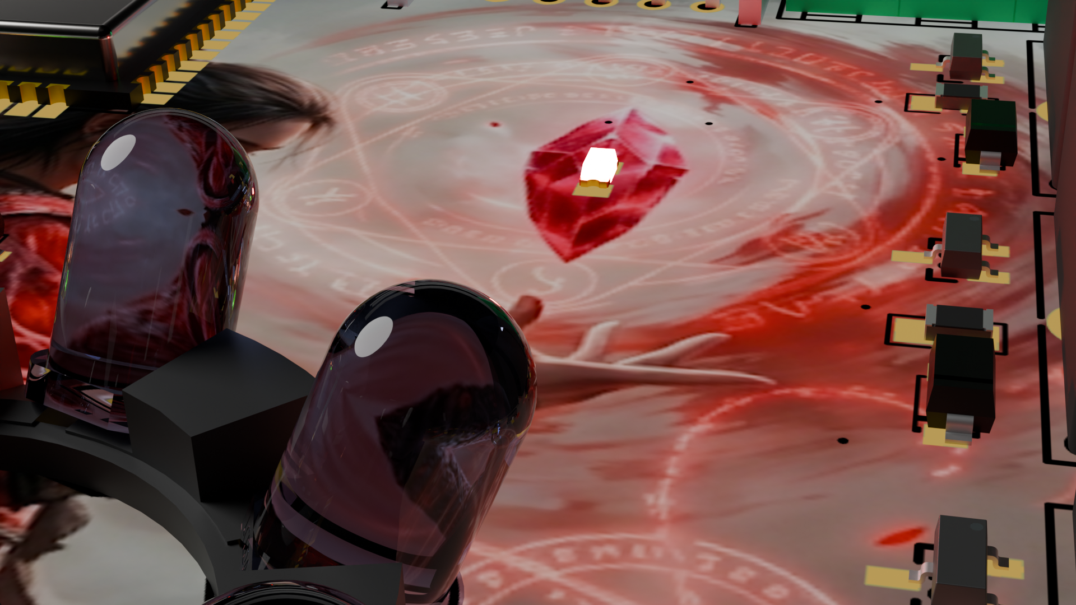
Render/ruby-render/0360.png
