dushyantyadav0303/Ruby-Home-Automation/Render/ruby-render/0367.png

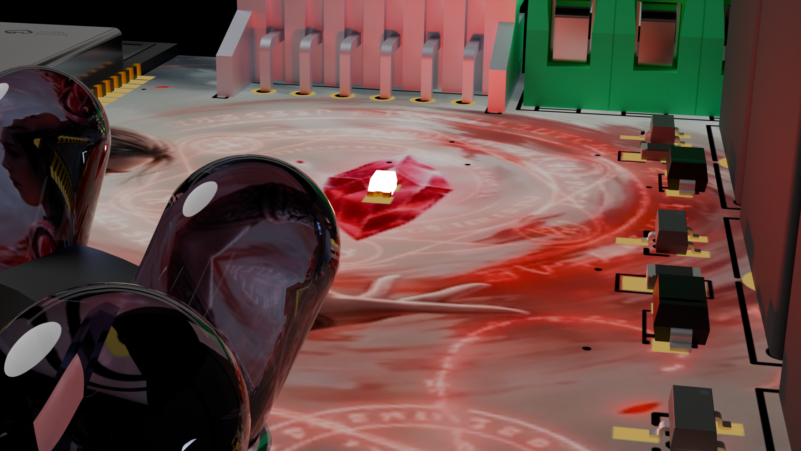
Render/ruby-render/0367.png
