dushyantyadav0303/Ruby-Home-Automation/Render/ruby-render/0373.png

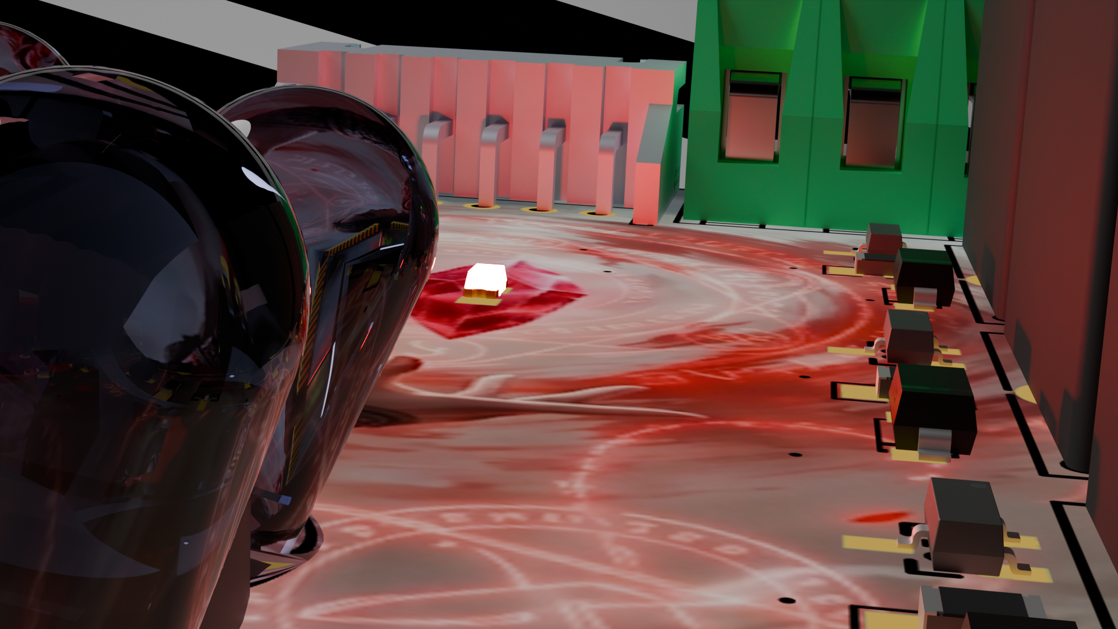
Render/ruby-render/0373.png
