dushyantyadav0303/Ruby-Home-Automation/Render/ruby-render/0379.png

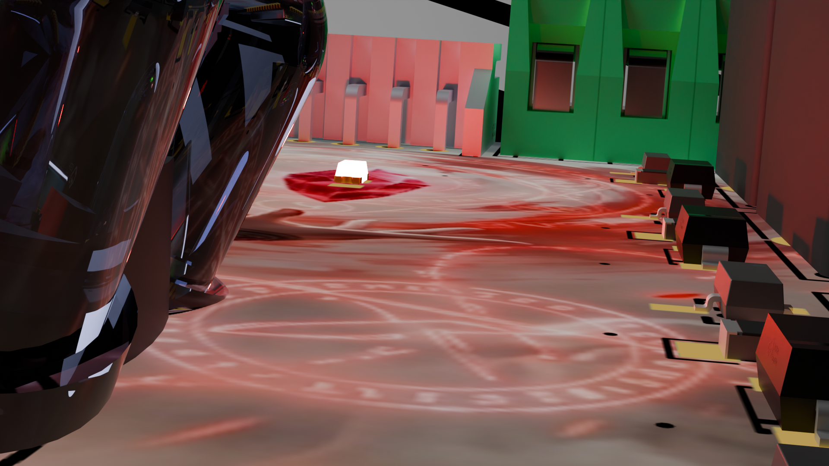
Render/ruby-render/0379.png
