dushyantyadav0303/Ruby-Home-Automation/Render/ruby-render/0386.png

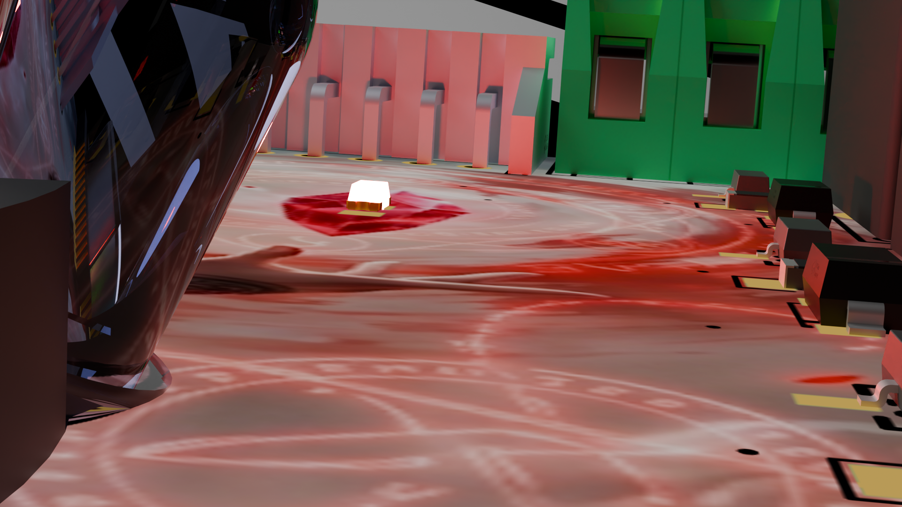
Render/ruby-render/0386.png
