dushyantyadav0303/Ruby-Home-Automation/Render/ruby-render/0387.png

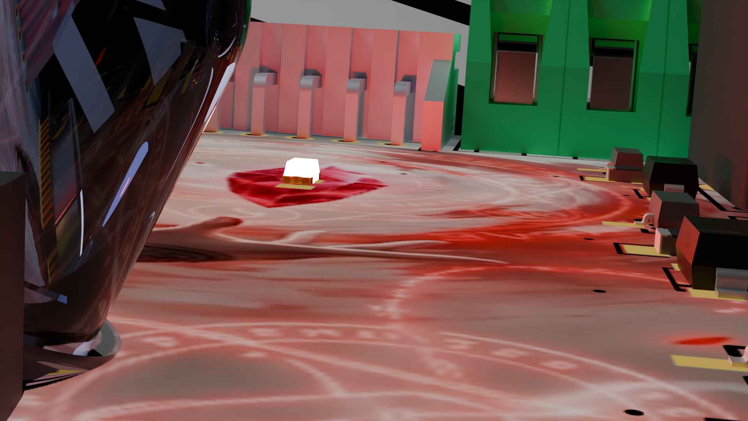
Render/ruby-render/0387.png
