dushyantyadav0303/Ruby-Home-Automation/Render/ruby-render/0391.png

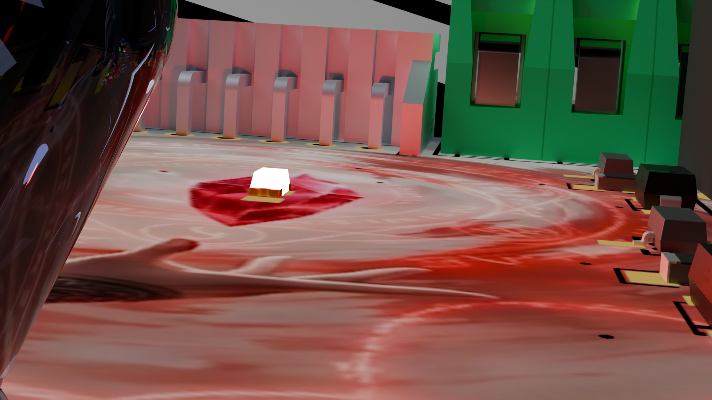
Render/ruby-render/0391.png
