dushyantyadav0303/Ruby-Home-Automation/Render/ruby-render/0394.png

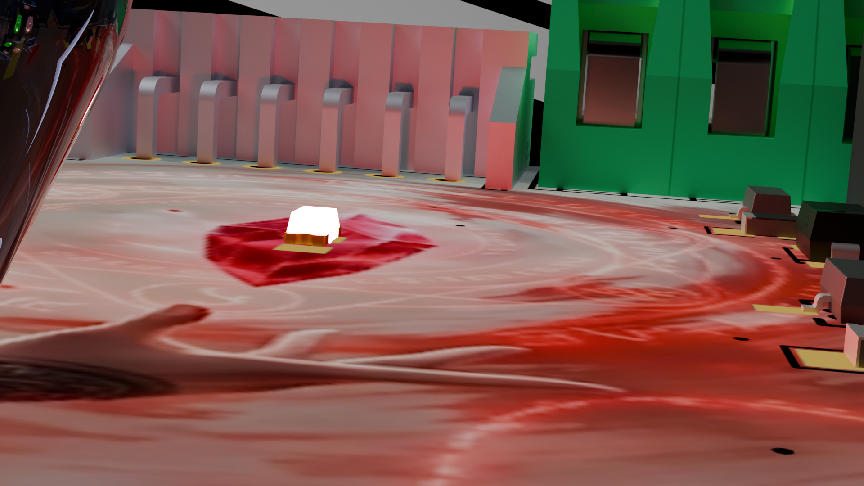
Render/ruby-render/0394.png
