dushyantyadav0303/Ruby-Home-Automation/Render/ruby-render/0397.png

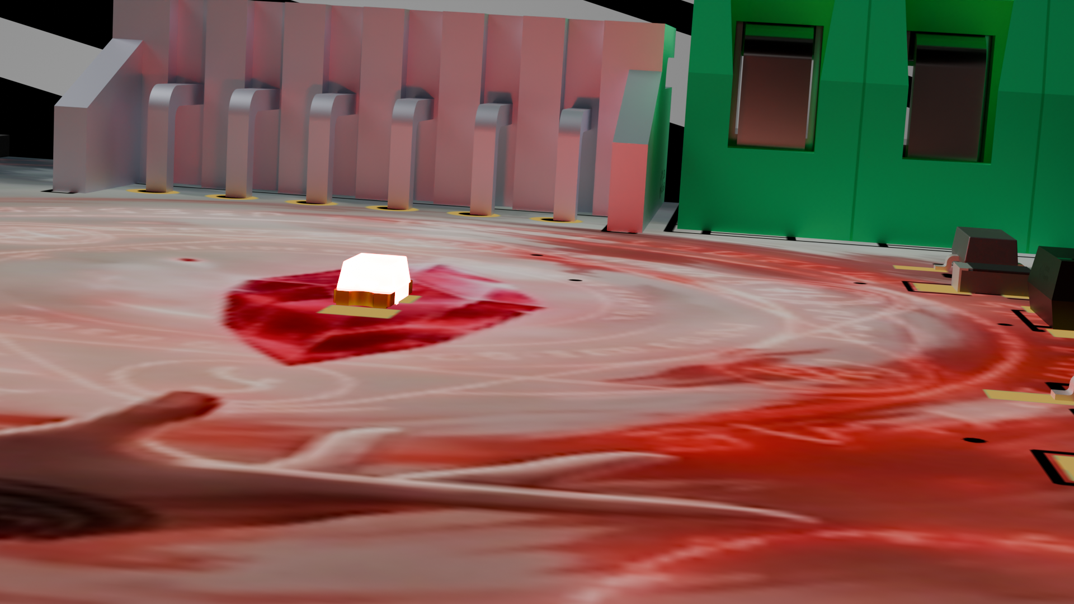
Render/ruby-render/0397.png
