dushyantyadav0303/Ruby-Home-Automation/Render/ruby-render/0401.png

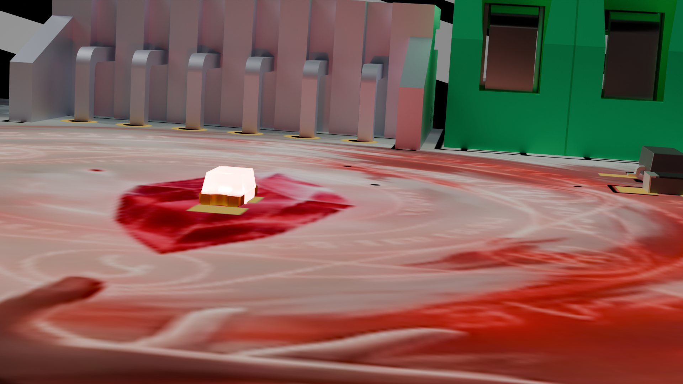
Render/ruby-render/0401.png
