dushyantyadav0303/Ruby-Home-Automation/Render/ruby-render/0404.png

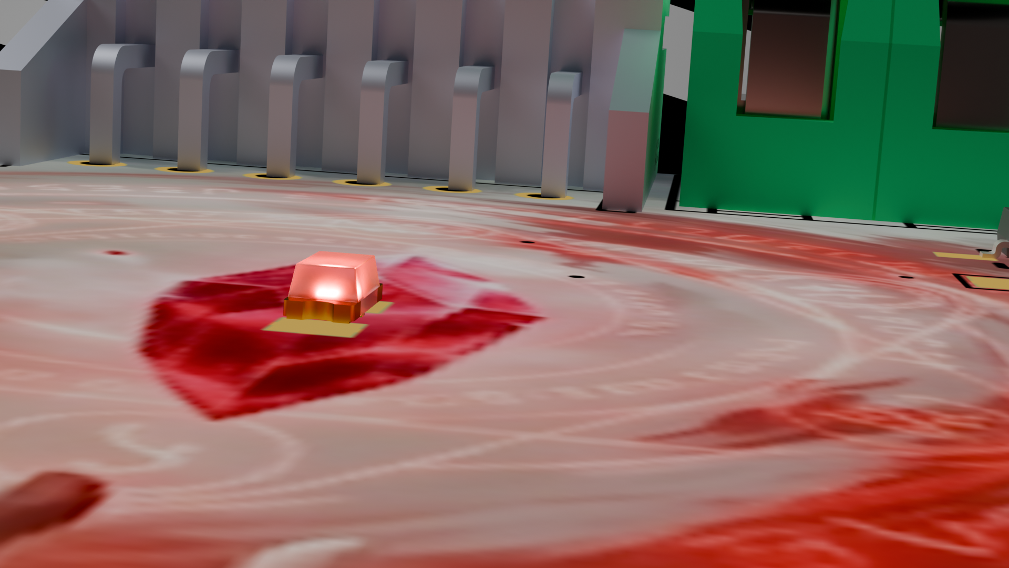
Render/ruby-render/0404.png
