dushyantyadav0303/Ruby-Home-Automation/Render/ruby-render/0406.png

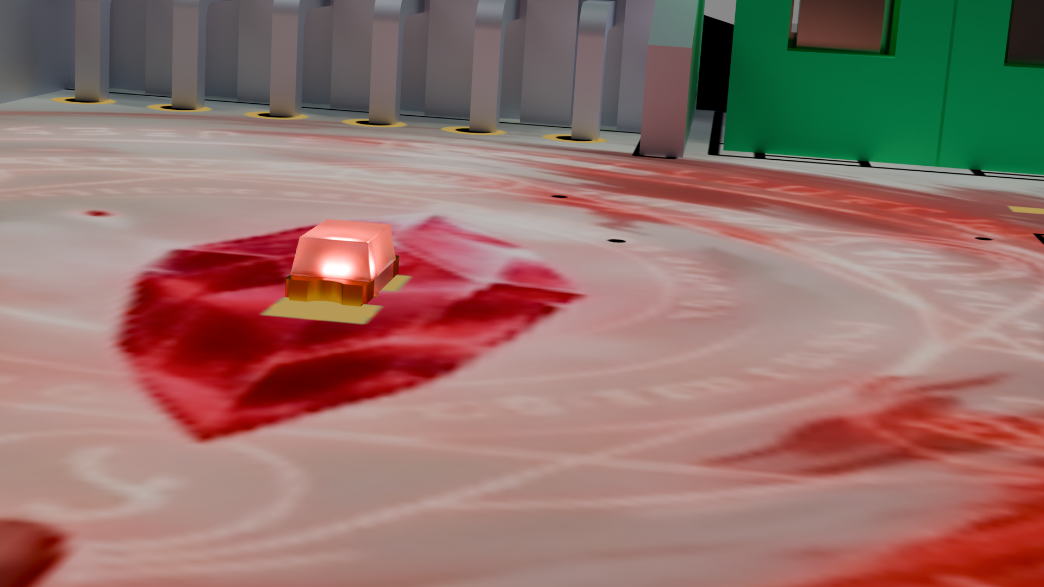
Render/ruby-render/0406.png
