dushyantyadav0303/Ruby-Home-Automation/Render/ruby-render/0407.png

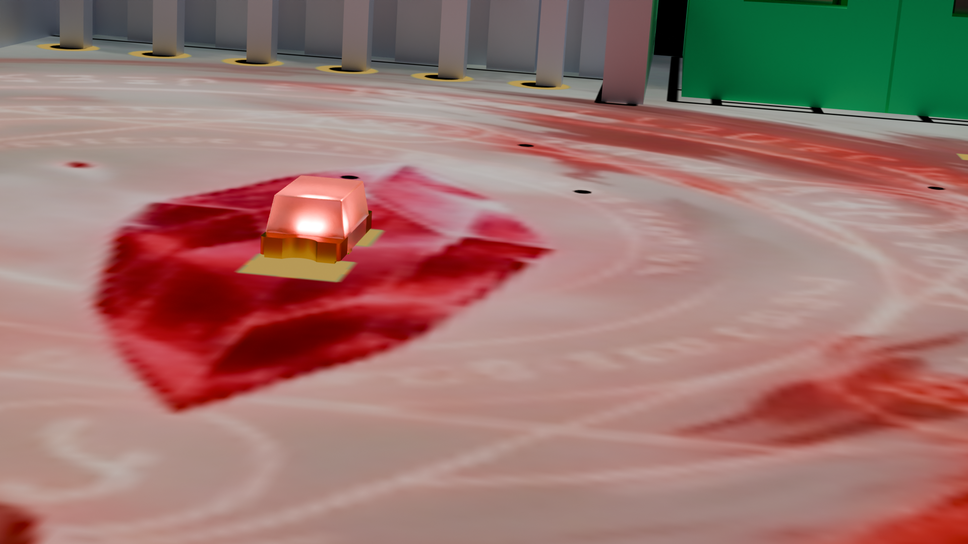
Render/ruby-render/0407.png
