dushyantyadav0303/Ruby-Home-Automation/Render/ruby-render/0408.png

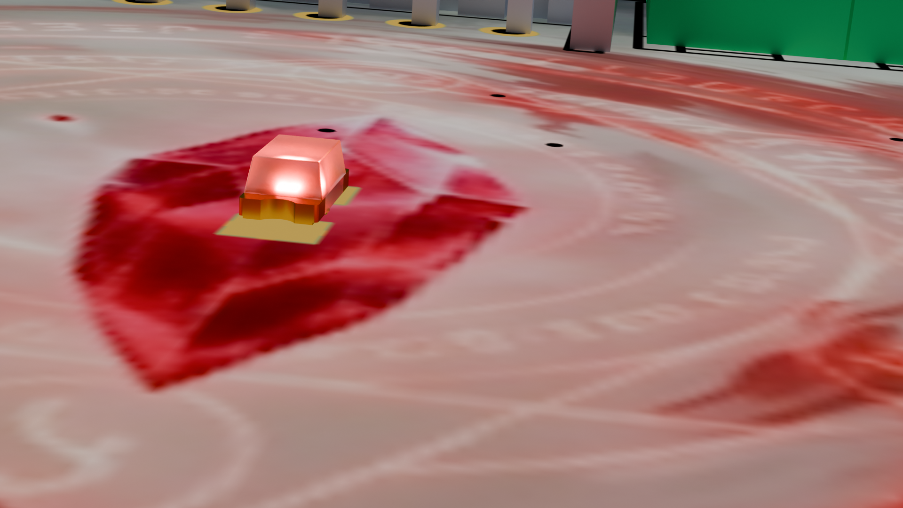
Render/ruby-render/0408.png
