dushyantyadav0303/Ruby-Home-Automation/Render/ruby-render/0409.png

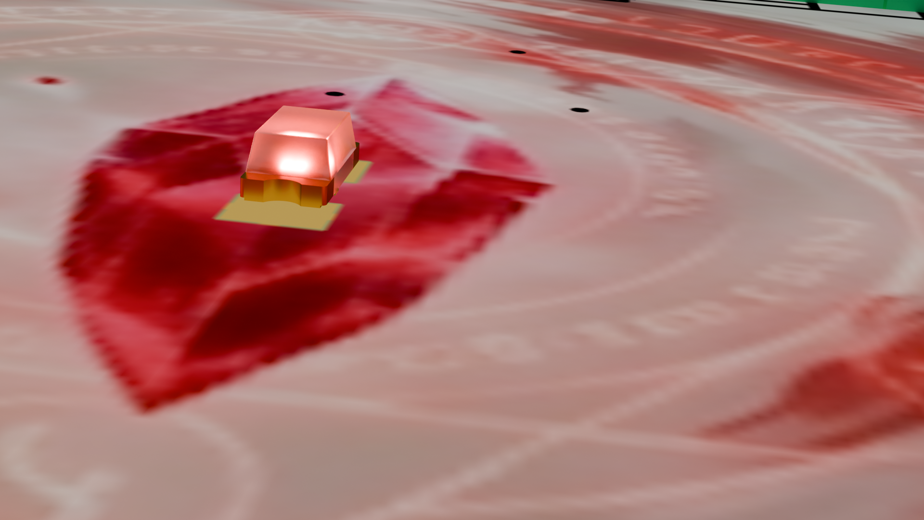
Render/ruby-render/0409.png
