dushyantyadav0303/Ruby-Home-Automation/Render/ruby-render/0414.png

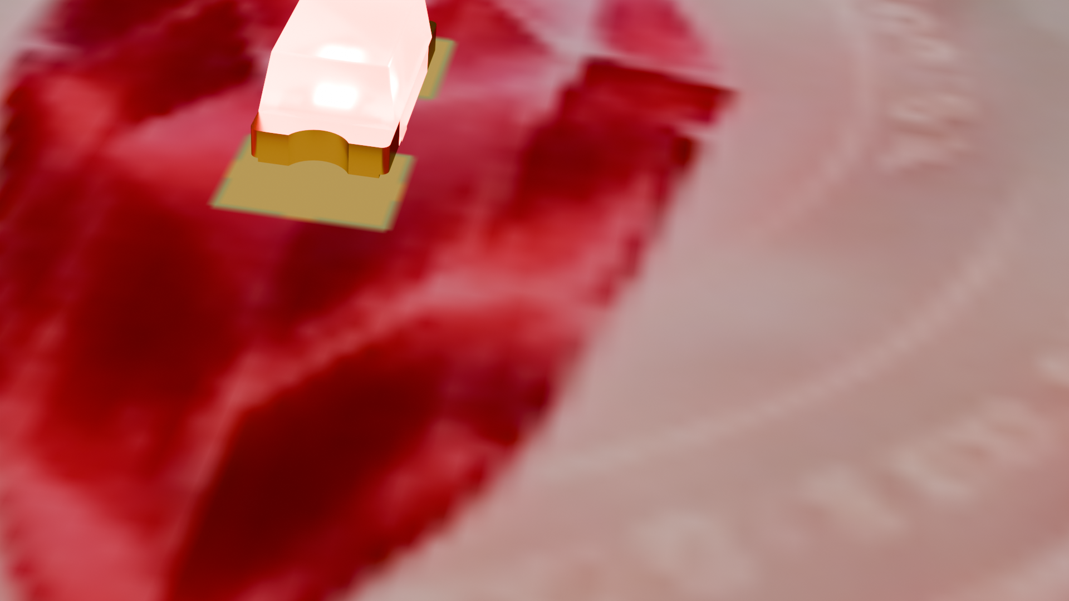
Render/ruby-render/0414.png
