dushyantyadav0303/Ruby-Home-Automation/Render/ruby-render/0417.png

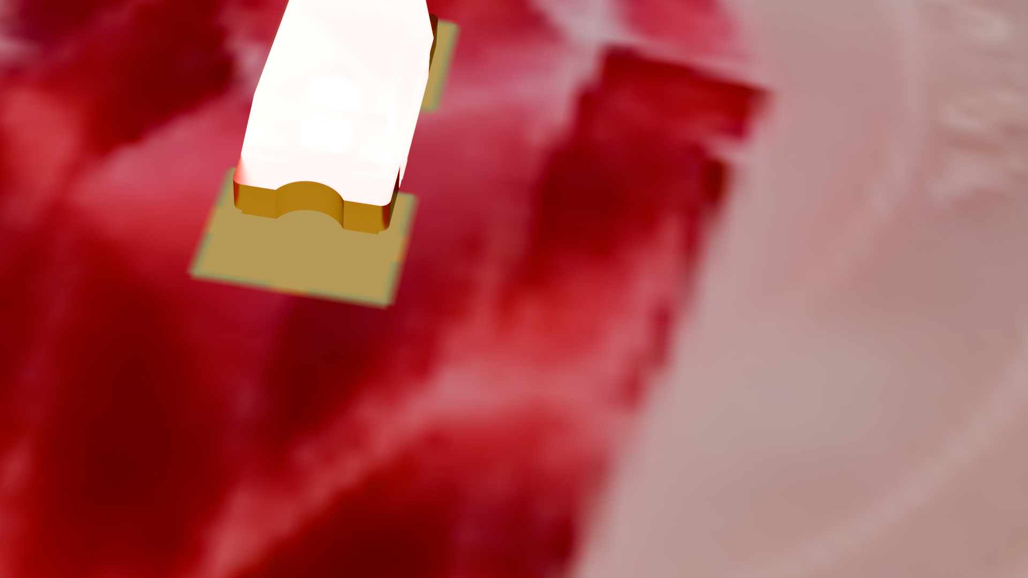
Render/ruby-render/0417.png
