dushyantyadav0303/Ruby-Home-Automation/Render/ruby-render/0418.png

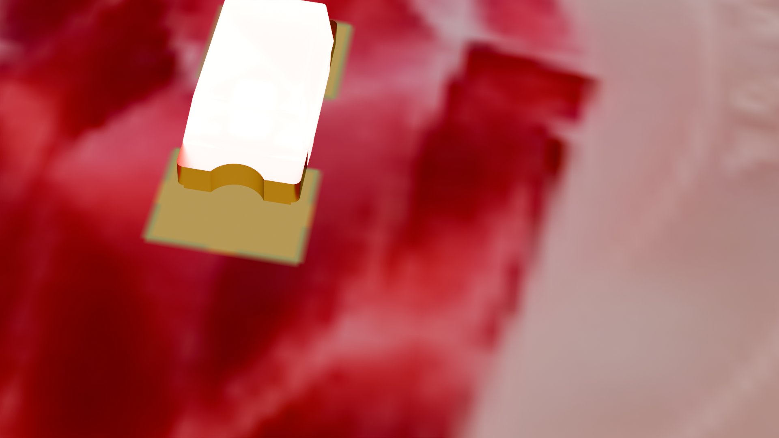
Render/ruby-render/0418.png
