dushyantyadav0303/Ruby-Home-Automation/Render/ruby-render/0419.png

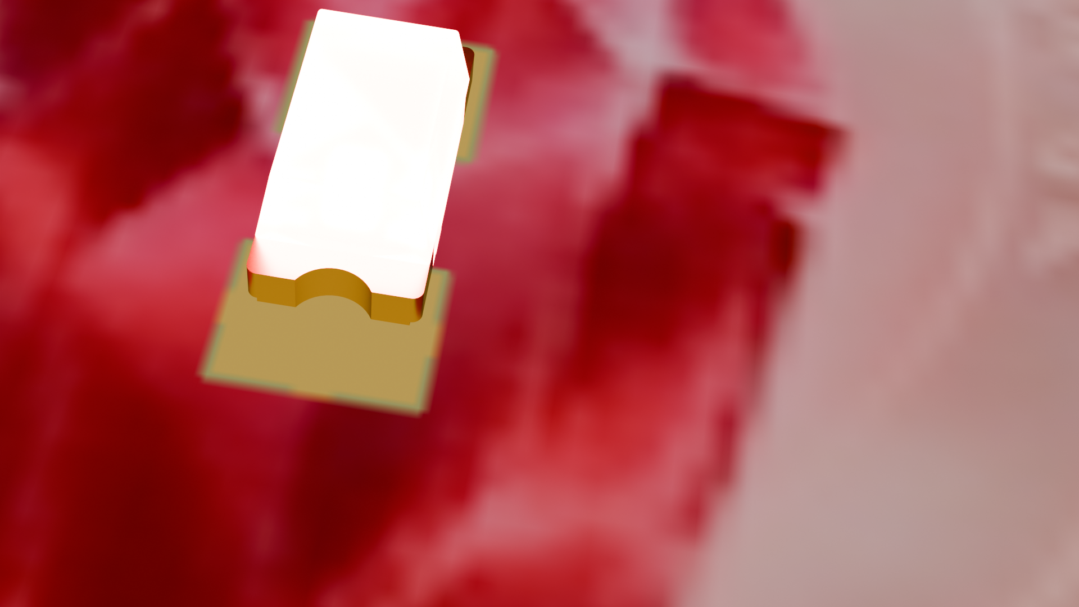
Render/ruby-render/0419.png
