dushyantyadav0303/Ruby-Home-Automation/Render/ruby-render/0421.png

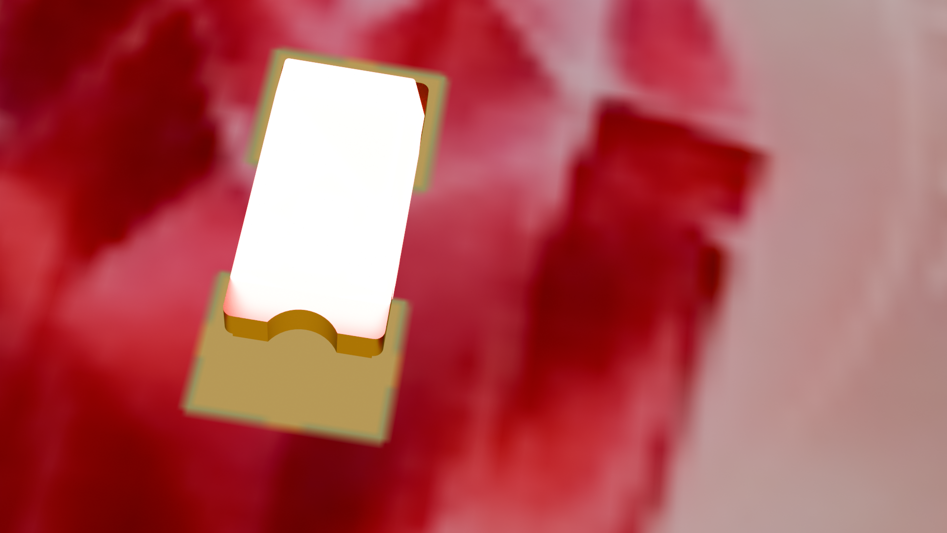
Render/ruby-render/0421.png
