dushyantyadav0303/Ruby-Home-Automation/Render/ruby-render/0424.png

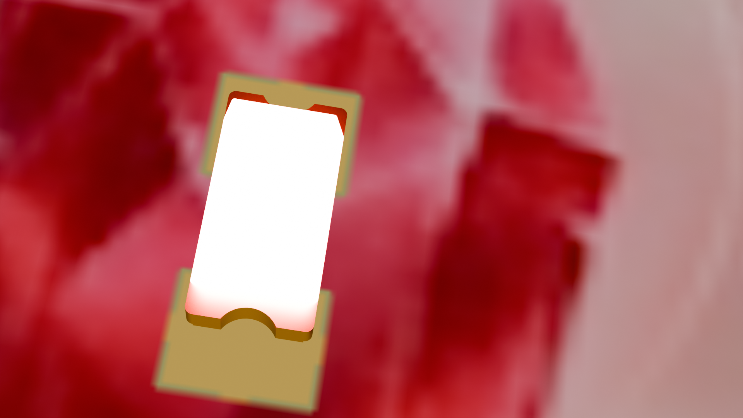
Render/ruby-render/0424.png
