dushyantyadav0303/Ruby-Home-Automation/Render/ruby-render/0428.png

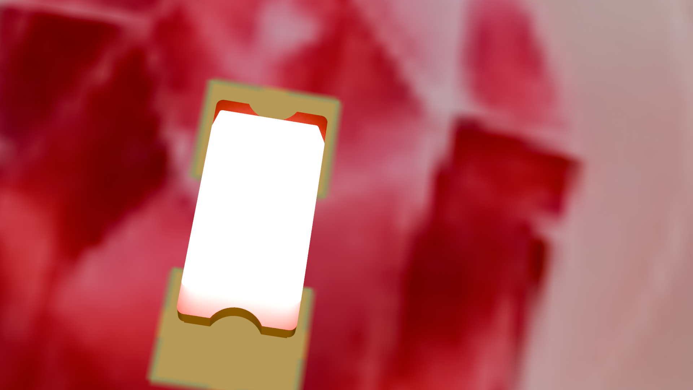
Render/ruby-render/0428.png
