dushyantyadav0303/Ruby-Home-Automation/Render/ruby-render/0446.png

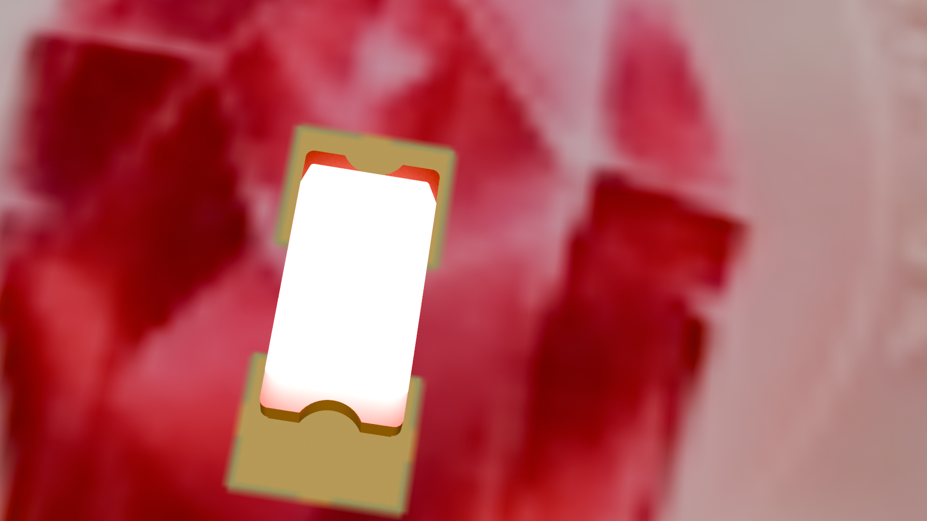
Render/ruby-render/0446.png
