dushyantyadav0303/Ruby-Home-Automation/Render/ruby-render/0449.png

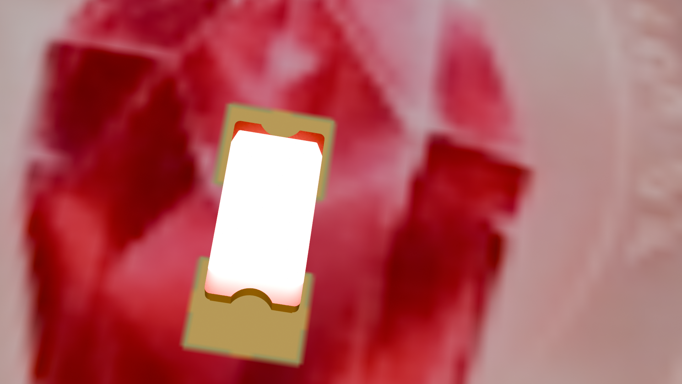
Render/ruby-render/0449.png
