dushyantyadav0303/Ruby-Home-Automation/Render/ruby-render/0451.png

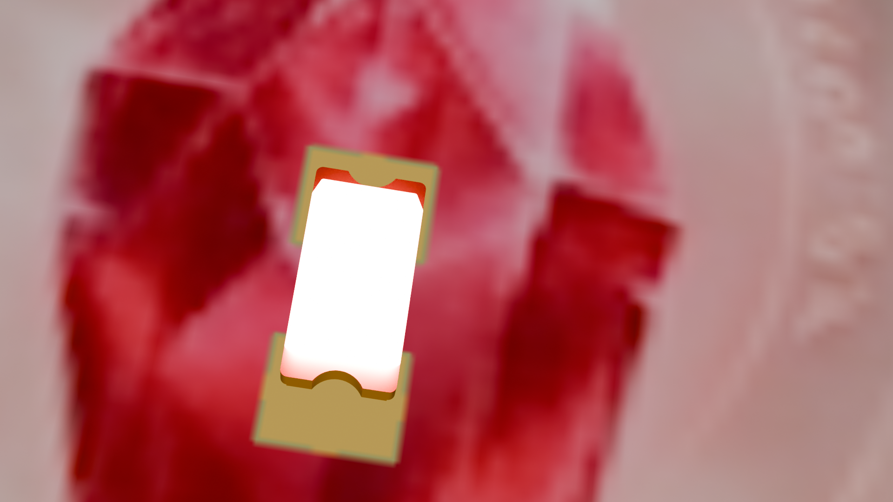
Render/ruby-render/0451.png
