dushyantyadav0303/Ruby-Home-Automation/Render/ruby-render/0452.png

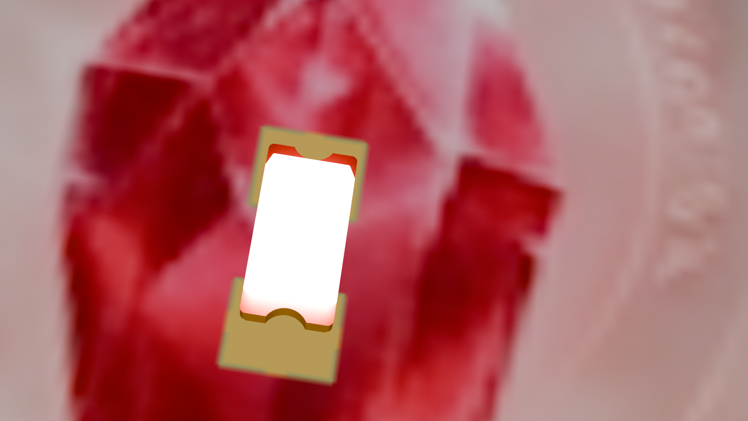
Render/ruby-render/0452.png
