dushyantyadav0303/Ruby-Home-Automation/Render/ruby-render/0454.png

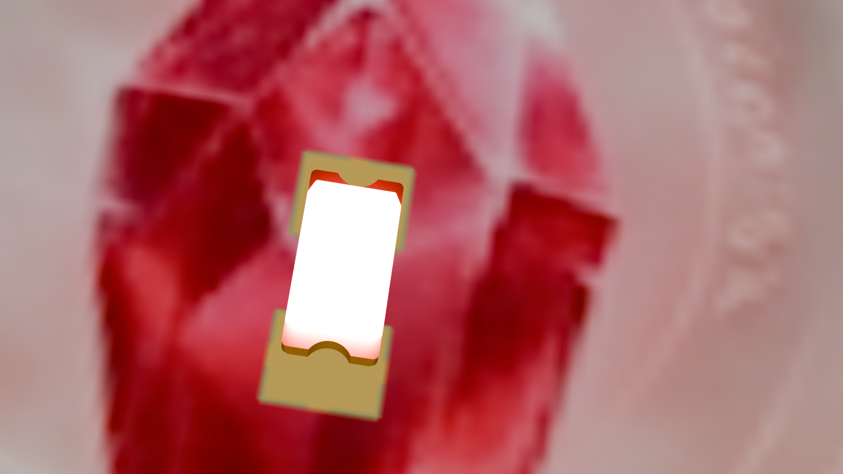
Render/ruby-render/0454.png
