dushyantyadav0303/Ruby-Home-Automation/Render/ruby-render/0455.png

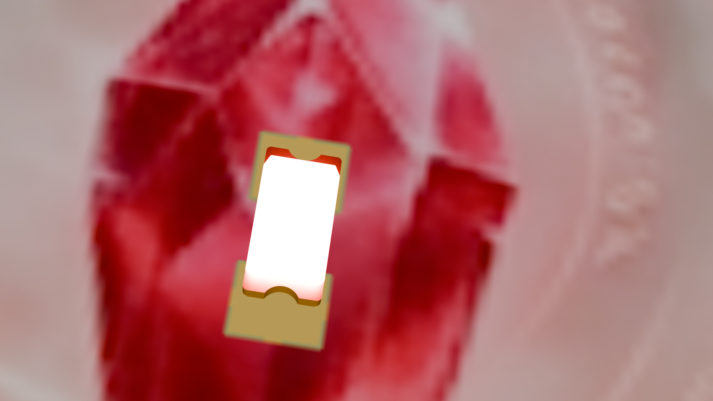
Render/ruby-render/0455.png
