dushyantyadav0303/Ruby-Home-Automation/Render/ruby-render/0458.png

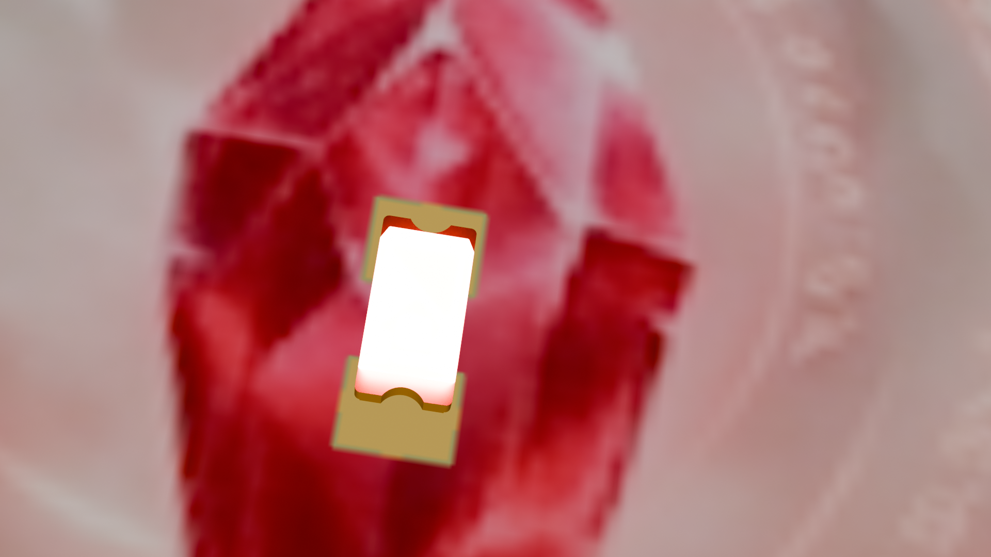
Render/ruby-render/0458.png
