dushyantyadav0303/Ruby-Home-Automation/Render/ruby-render/0459.png

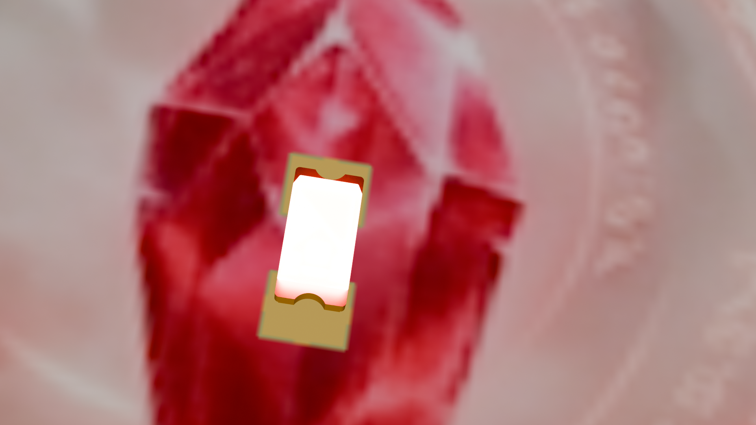
Render/ruby-render/0459.png
