dushyantyadav0303/Ruby-Home-Automation/Render/ruby-render/0460.png

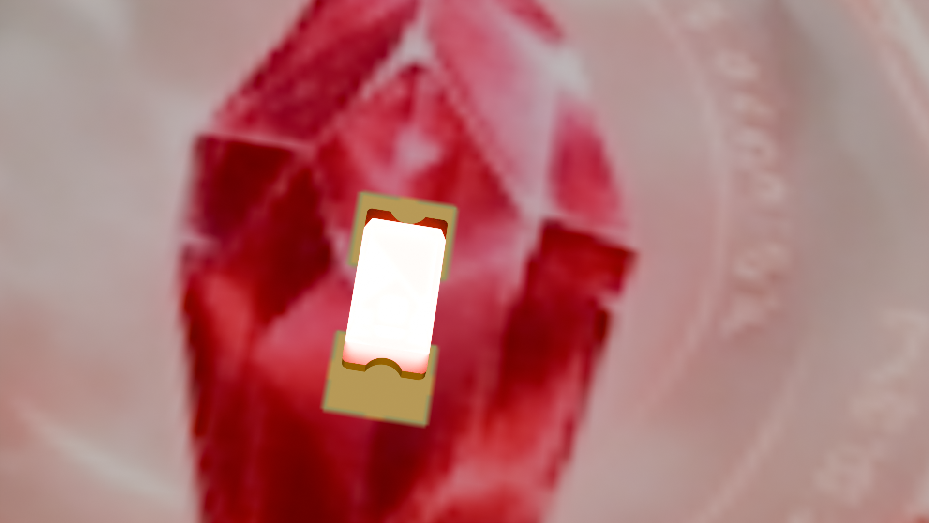
Render/ruby-render/0460.png
