dushyantyadav0303/Ruby-Home-Automation/Render/ruby-render/0467.png

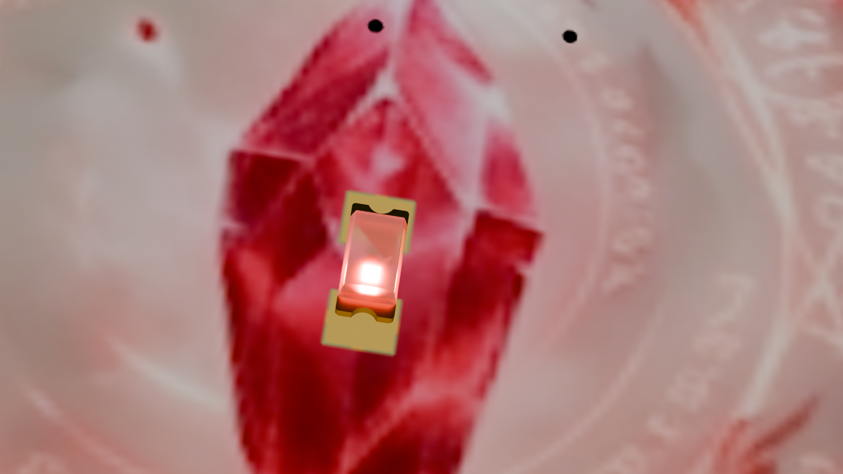
Render/ruby-render/0467.png
