dushyantyadav0303/Ruby-Home-Automation/Render/ruby-render/0469.png

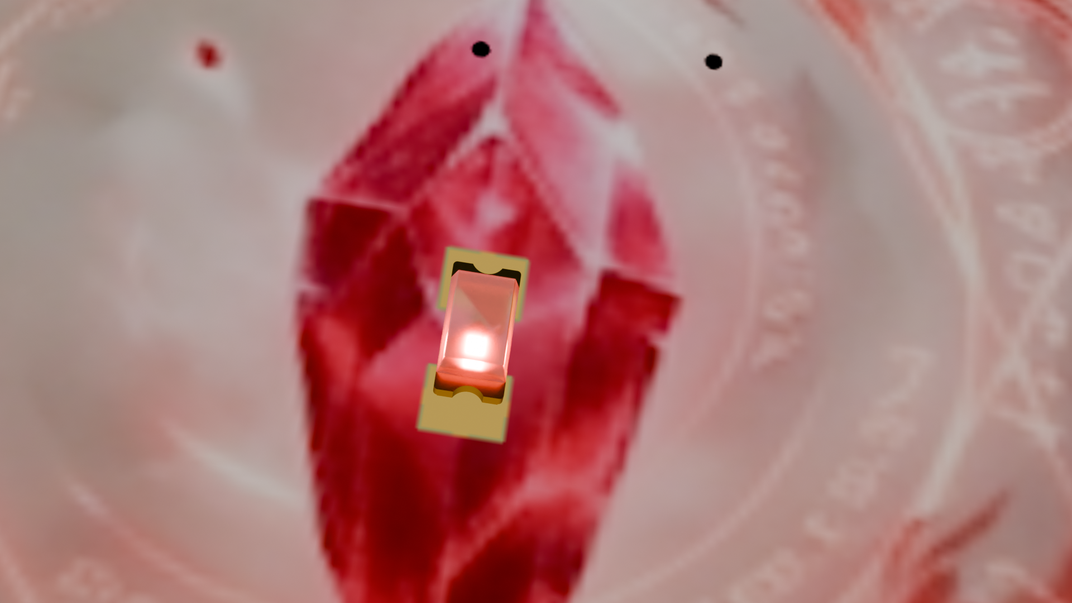
Render/ruby-render/0469.png
