dushyantyadav0303/Ruby-Home-Automation/Render/ruby-render/0473.png

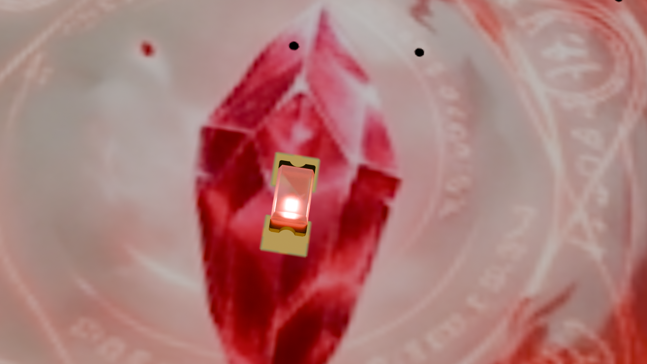
Render/ruby-render/0473.png
