dushyantyadav0303/Ruby-Home-Automation/Render/ruby-render/0480.png

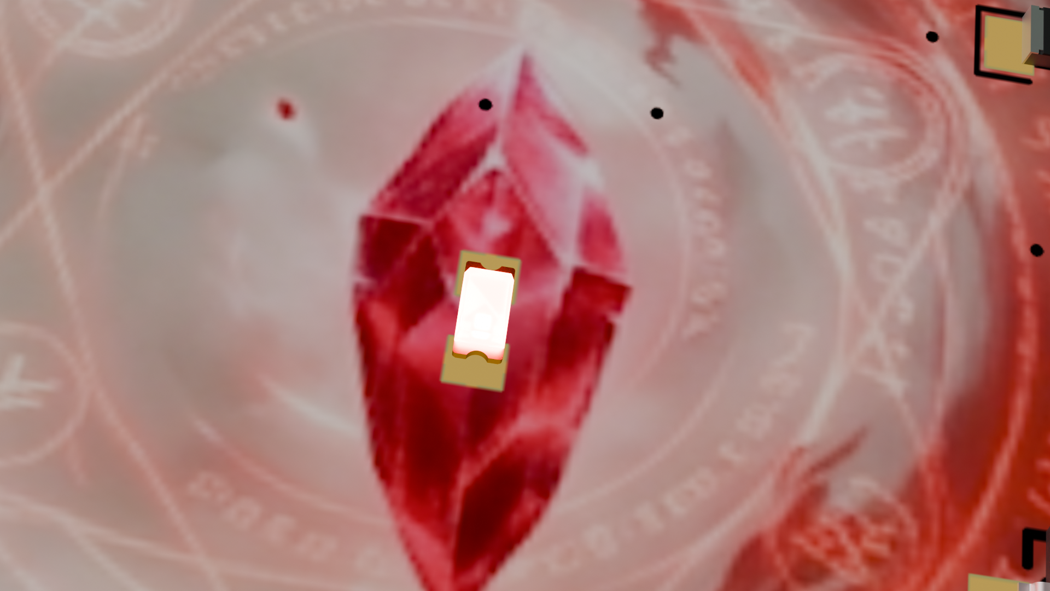
Render/ruby-render/0480.png
