dushyantyadav0303/Ruby-Home-Automation/Render/ruby-render/0482.png

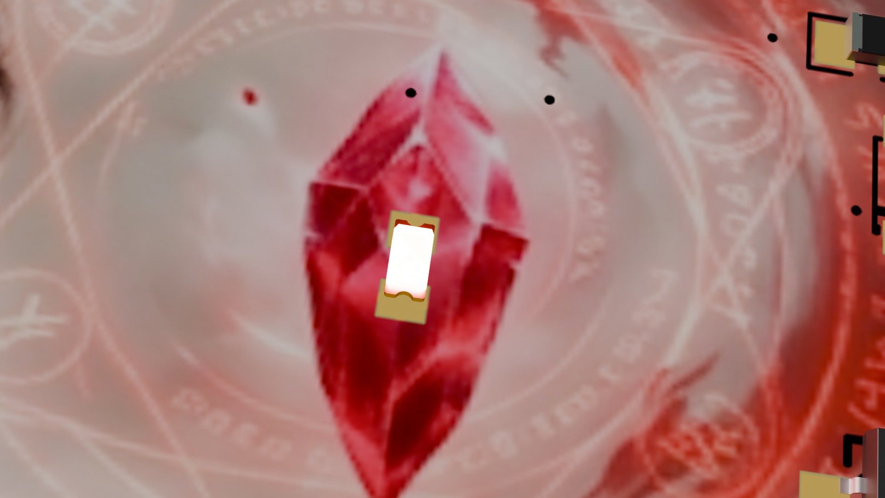
Render/ruby-render/0482.png
