dushyantyadav0303/Ruby-Home-Automation/Render/ruby-render/0487.png

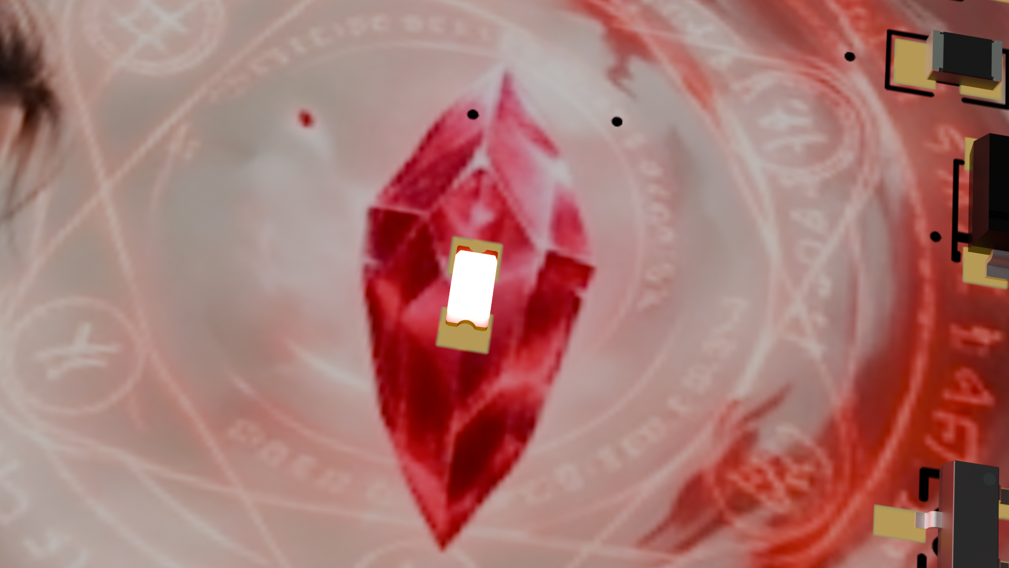
Render/ruby-render/0487.png
