dushyantyadav0303/Ruby-Home-Automation/Render/ruby-render/0491.png

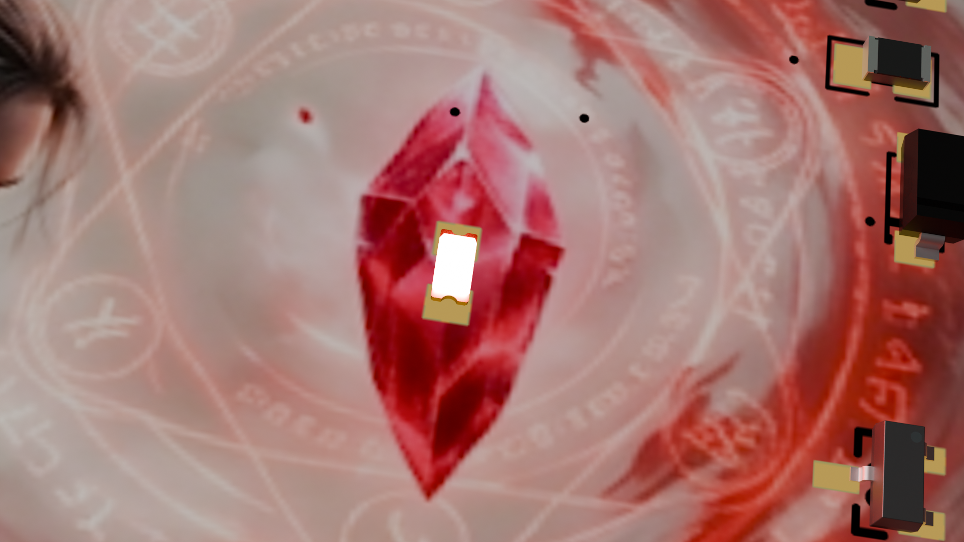
Render/ruby-render/0491.png
