dushyantyadav0303/Ruby-Home-Automation/Render/ruby-render/0497.png

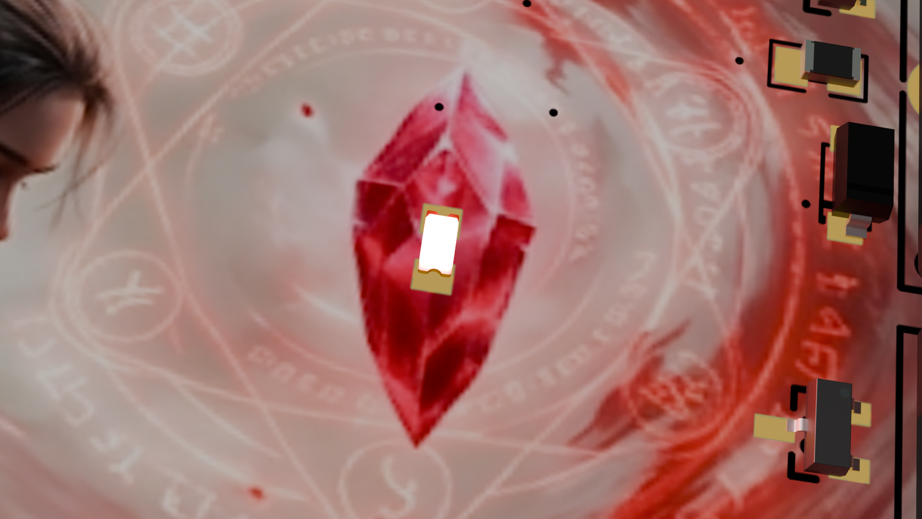
Render/ruby-render/0497.png
