dushyantyadav0303/Ruby-Home-Automation/Render/ruby-render/0500.png

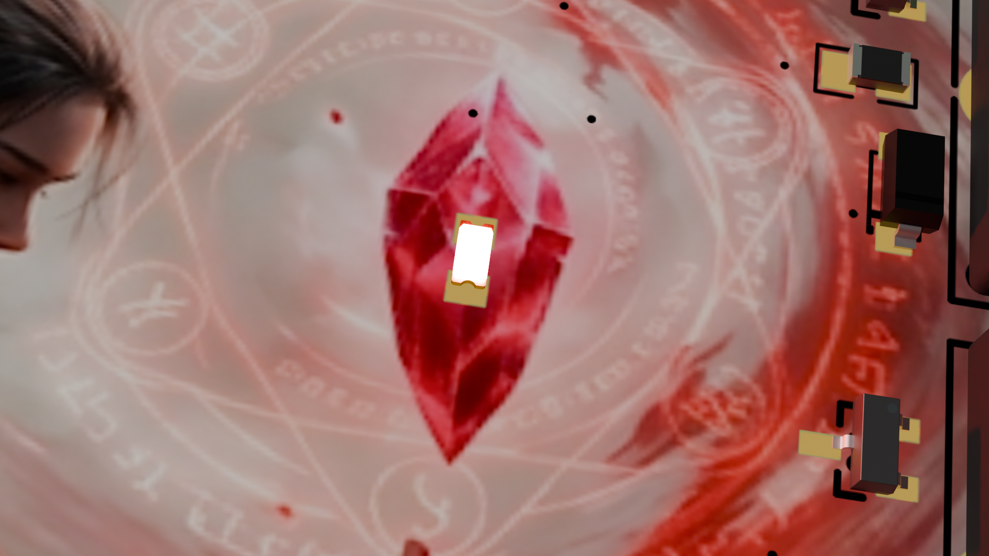
Render/ruby-render/0500.png
