dushyantyadav0303/Ruby-Home-Automation/Render/ruby-render/0504.png

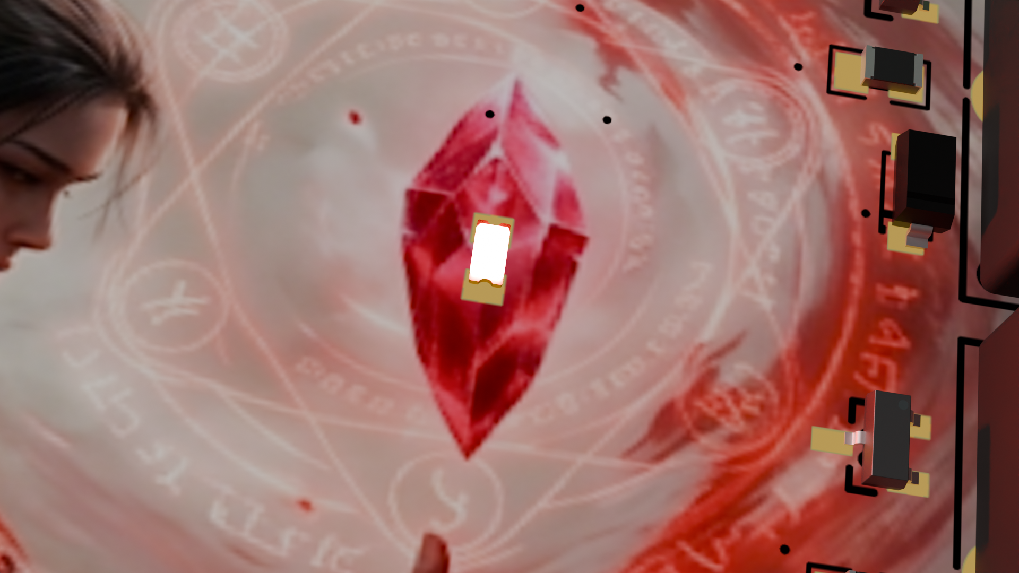
Render/ruby-render/0504.png
