dushyantyadav0303/Ruby-Home-Automation/Render/ruby-render/0514.png

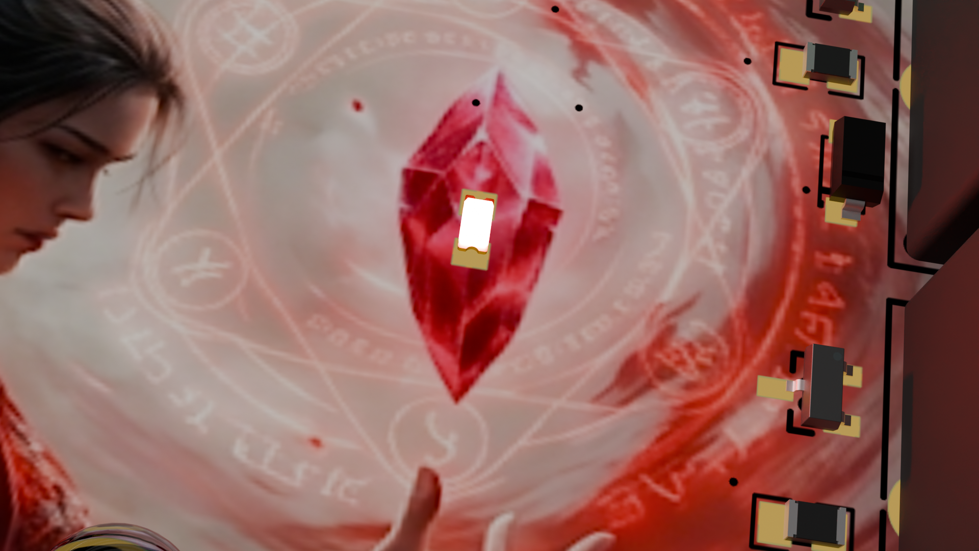
Render/ruby-render/0514.png
