dushyantyadav0303/Ruby-Home-Automation/Render/ruby-render/0522.png

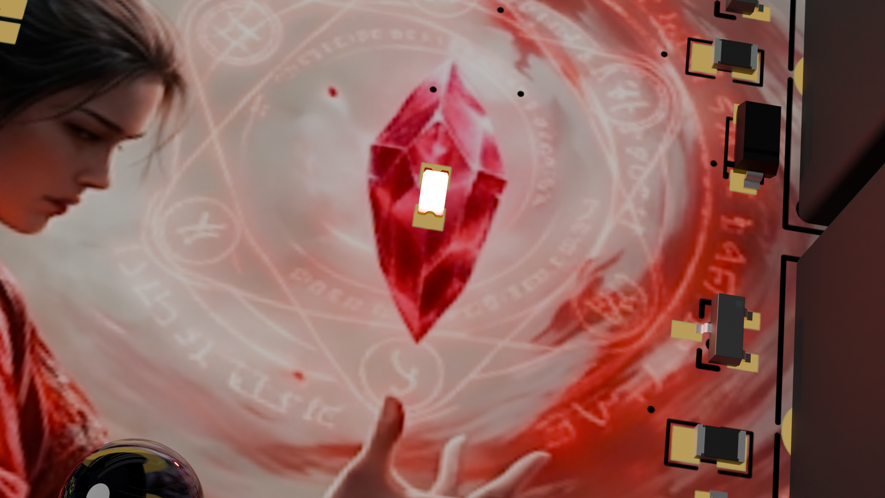
Render/ruby-render/0522.png
