dushyantyadav0303/Ruby-Home-Automation/Render/ruby-render/0535.png

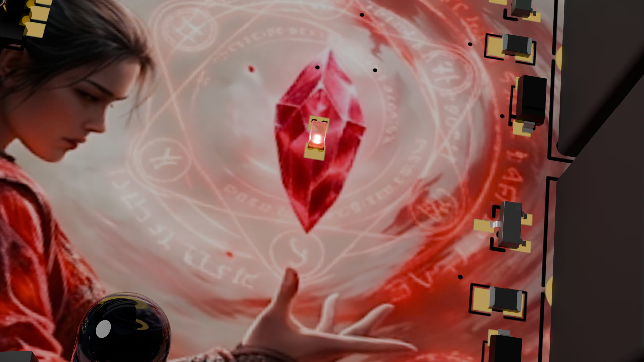
Render/ruby-render/0535.png
