dushyantyadav0303/Ruby-Home-Automation/Render/ruby-render/0540.png

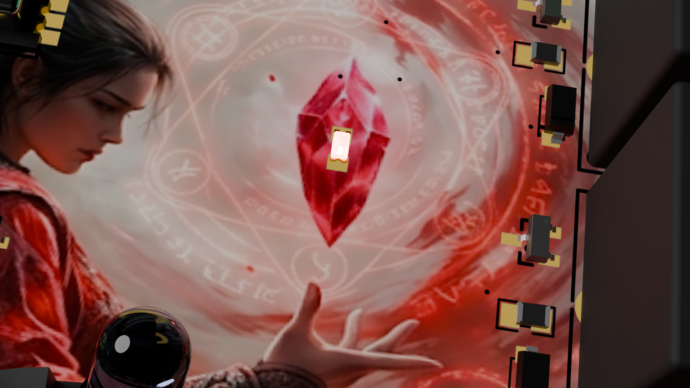
Render/ruby-render/0540.png
