dushyantyadav0303/Ruby-Home-Automation/Render/ruby-render/0545.png

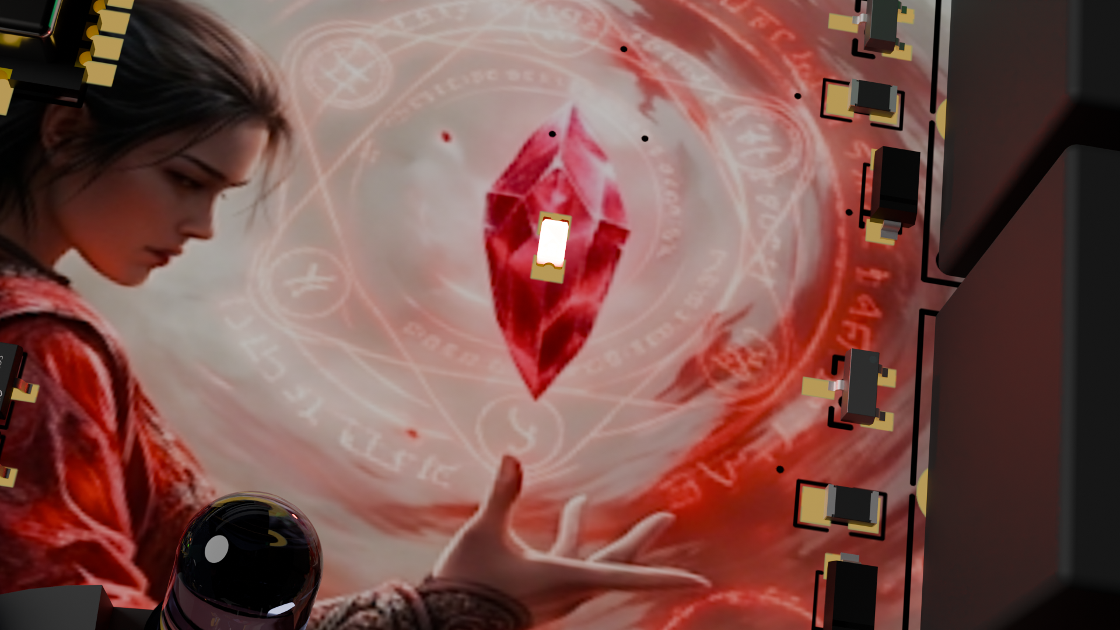
Render/ruby-render/0545.png
