dushyantyadav0303/Ruby-Home-Automation/Render/ruby-render/0555.png

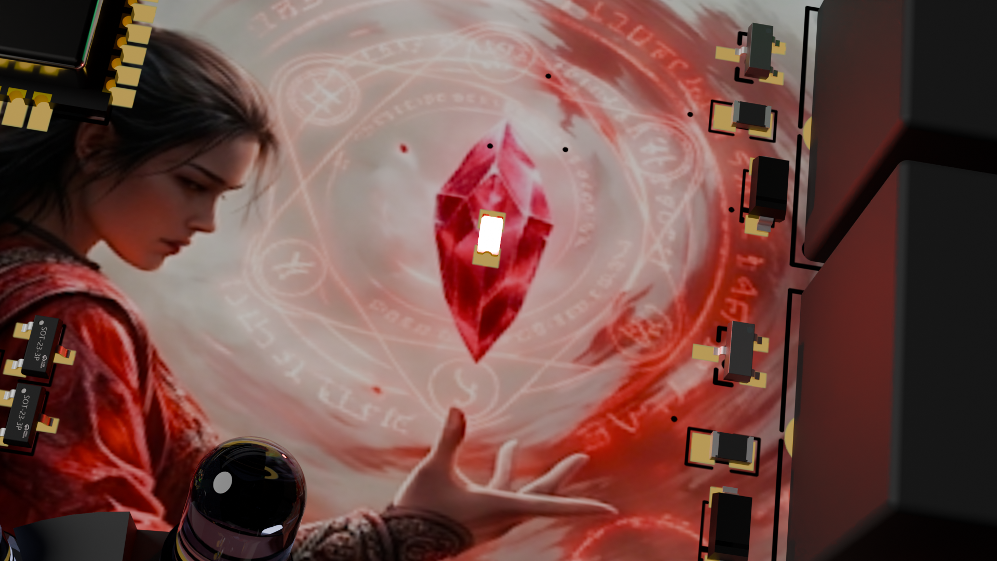
Render/ruby-render/0555.png
