dushyantyadav0303/Ruby-Home-Automation/Render/ruby-render/0562.png

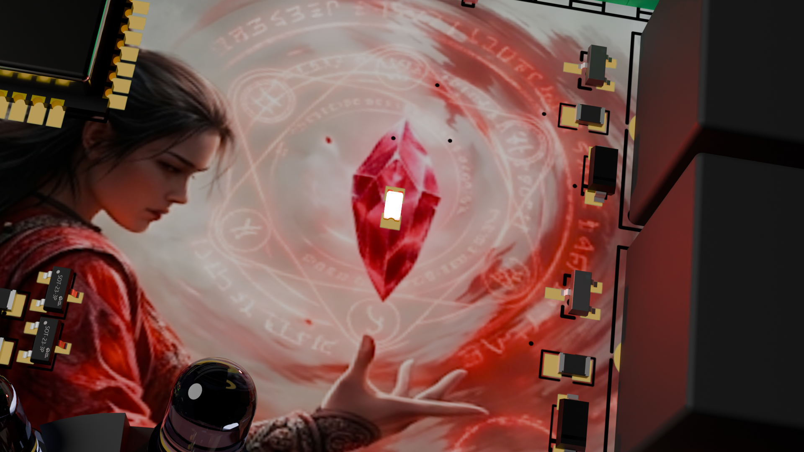
Render/ruby-render/0562.png
