dushyantyadav0303/Ruby-Home-Automation/Render/ruby-render/0570.png

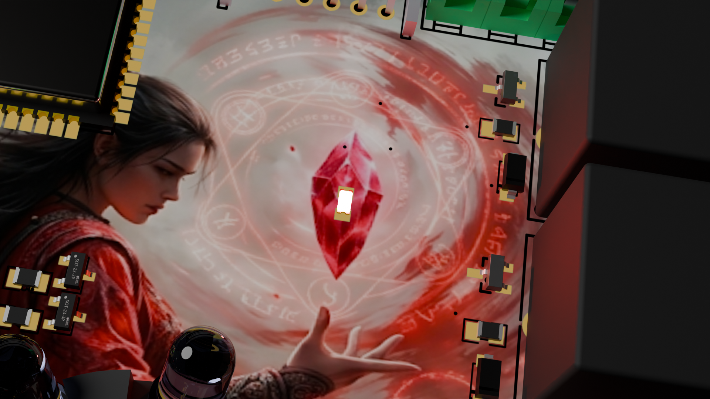
Render/ruby-render/0570.png
