dushyantyadav0303/Ruby-Home-Automation/Render/ruby-render/0575.png

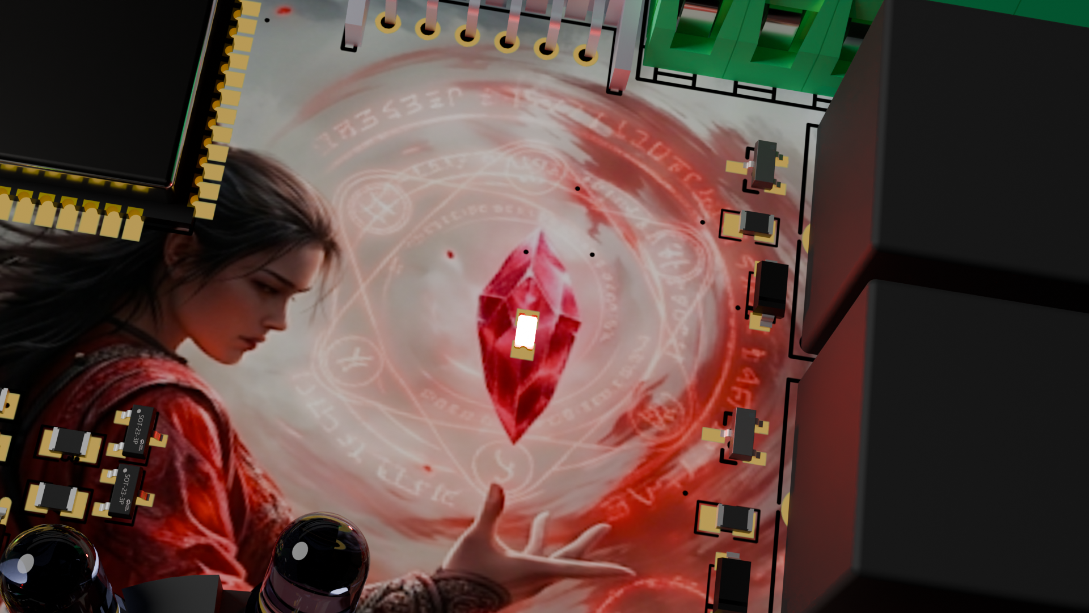
Render/ruby-render/0575.png
