dushyantyadav0303/Ruby-Home-Automation/Render/ruby-render/0578.png

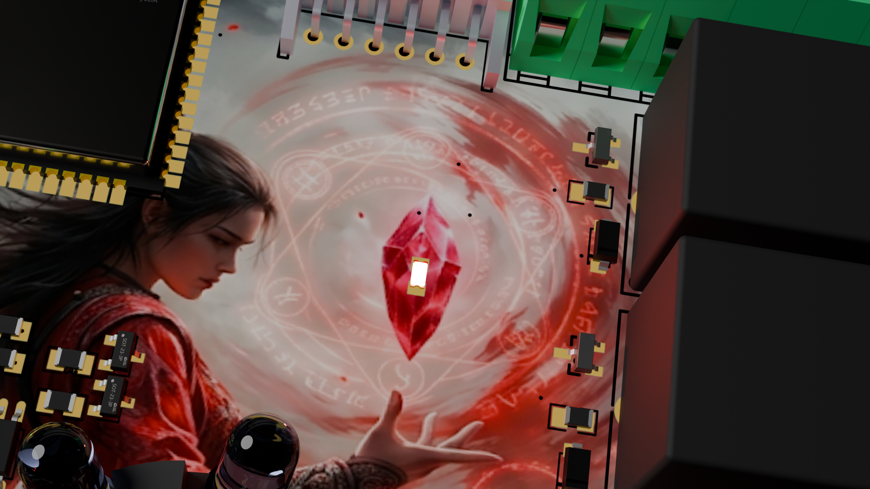
Render/ruby-render/0578.png
