dushyantyadav0303/Ruby-Home-Automation/Render/ruby-render/0582.png

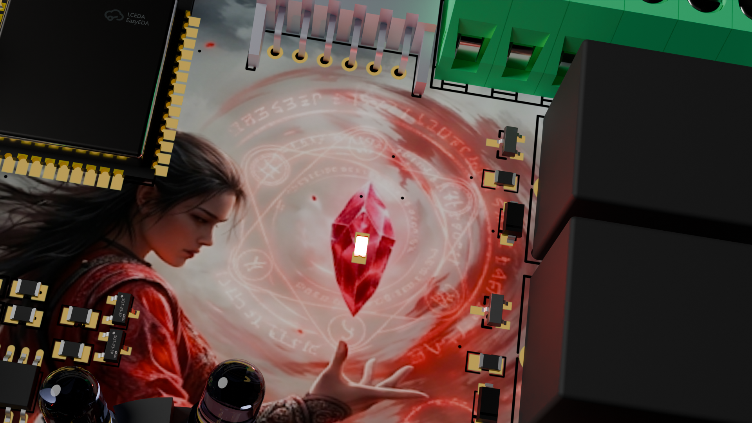
Render/ruby-render/0582.png
