dushyantyadav0303/Ruby-Home-Automation/Render/ruby-render/0584.png

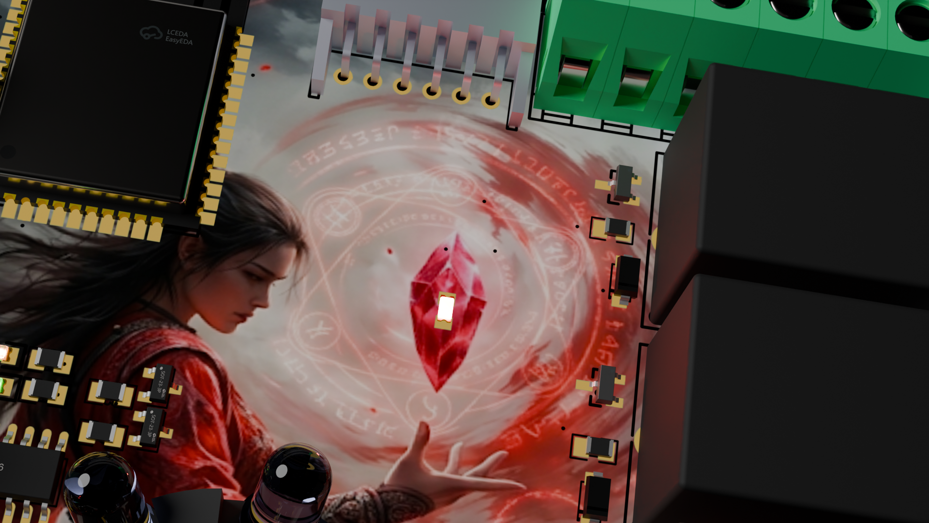
Render/ruby-render/0584.png
