dushyantyadav0303/Ruby-Home-Automation/Render/ruby-render/0588.png

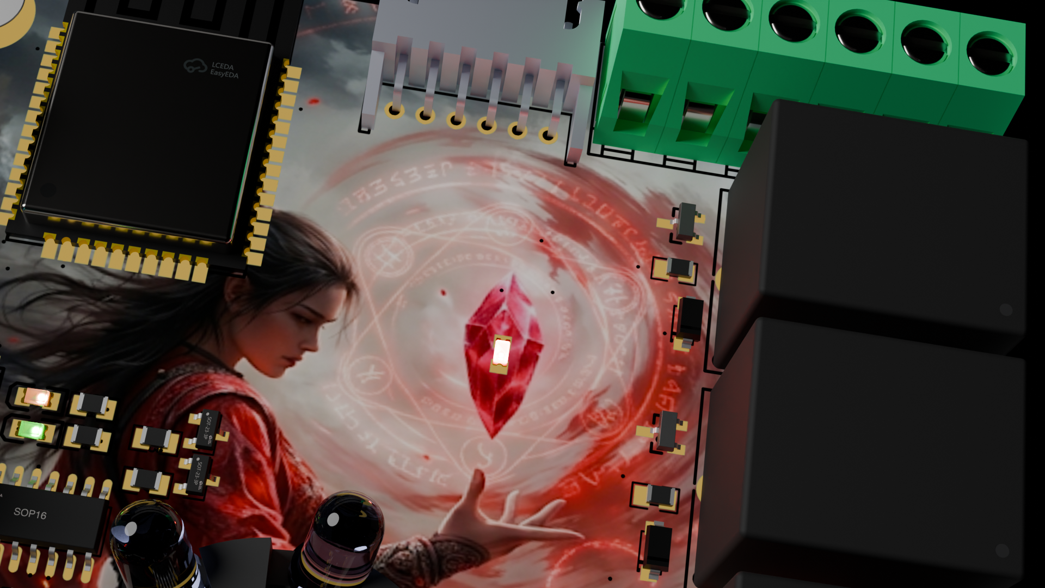
Render/ruby-render/0588.png
