dushyantyadav0303/Ruby-Home-Automation/Render/ruby-render/0594.png

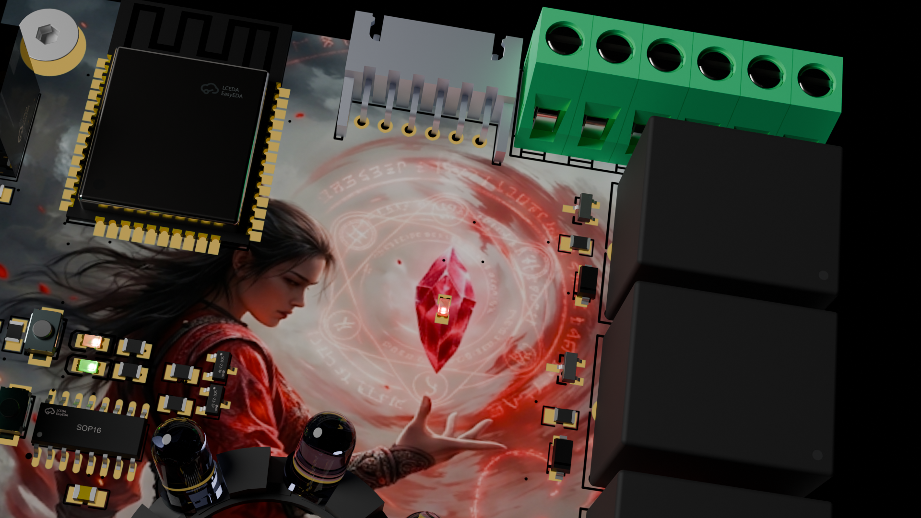
Render/ruby-render/0594.png
