dushyantyadav0303/Ruby-Home-Automation/Render/ruby-render/0599.png

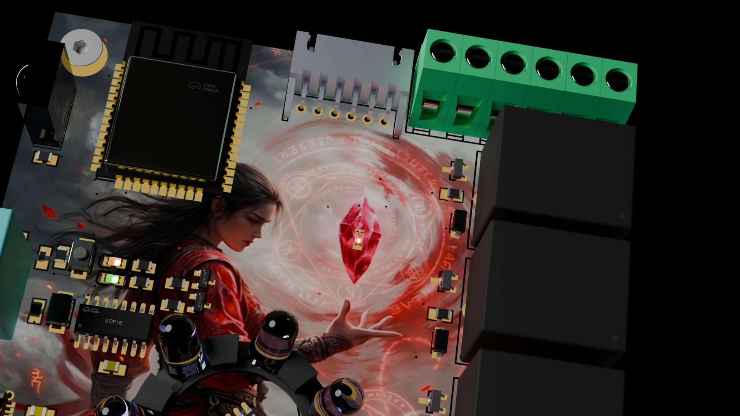
Render/ruby-render/0599.png
