dushyantyadav0303/Ruby-Home-Automation/Render/ruby-render/0604.png

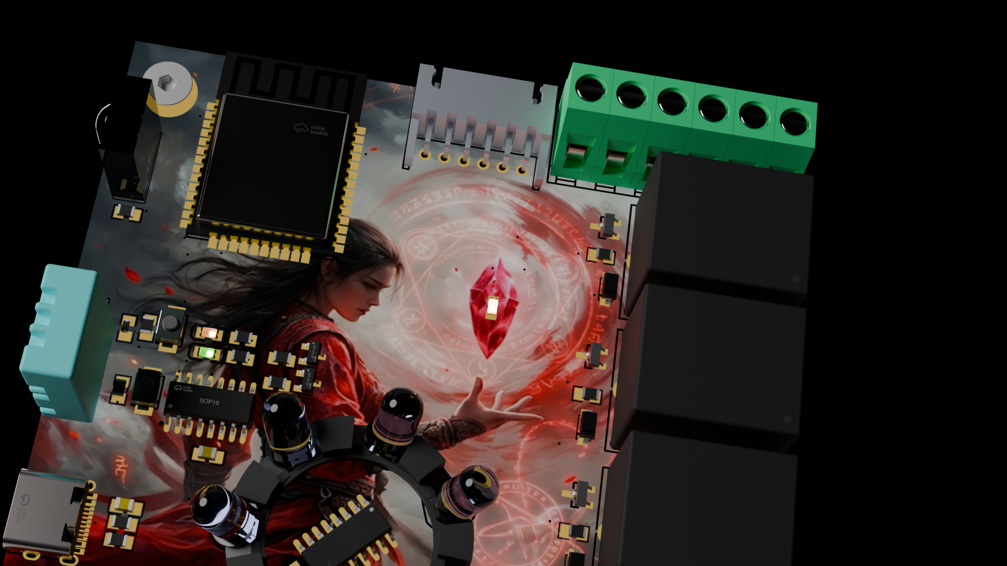
Render/ruby-render/0604.png
