dushyantyadav0303/Ruby-Home-Automation/Render/ruby-render/0606.png

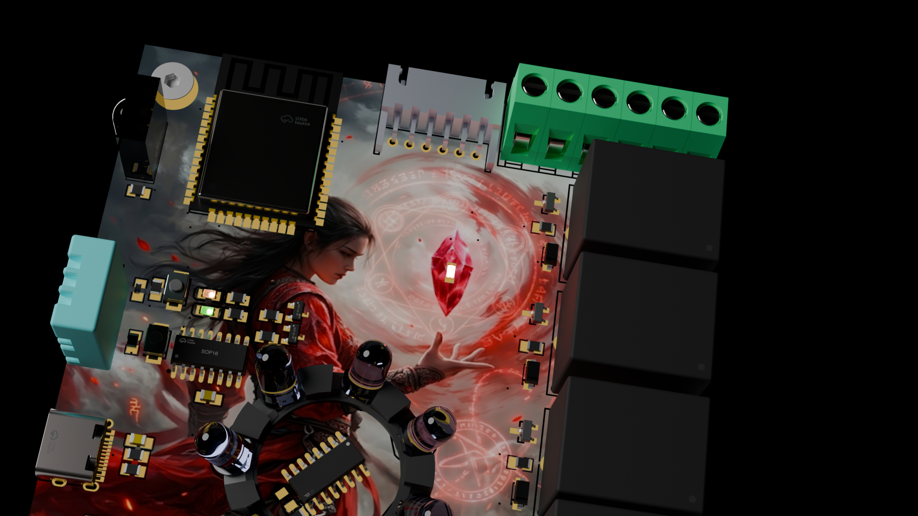
Render/ruby-render/0606.png
