dushyantyadav0303/Ruby-Home-Automation/Render/ruby-render/0608.png

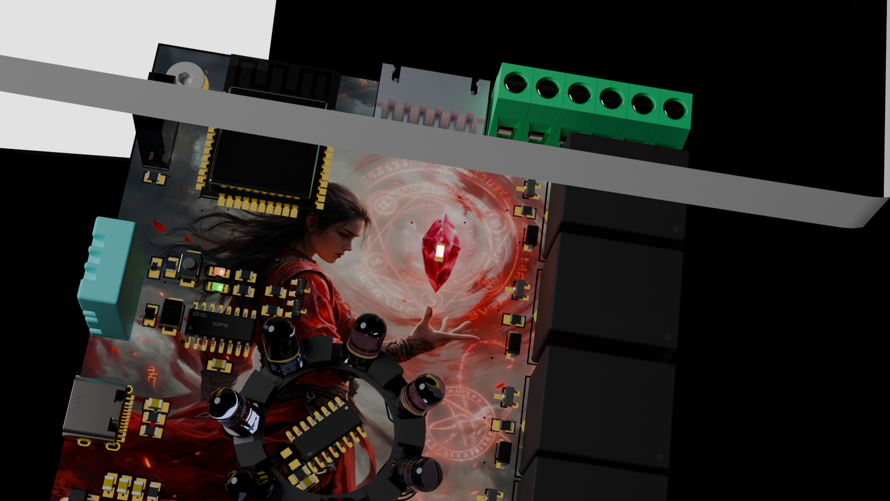
Render/ruby-render/0608.png
