dushyantyadav0303/Ruby-Home-Automation/Render/ruby-render/0611.png

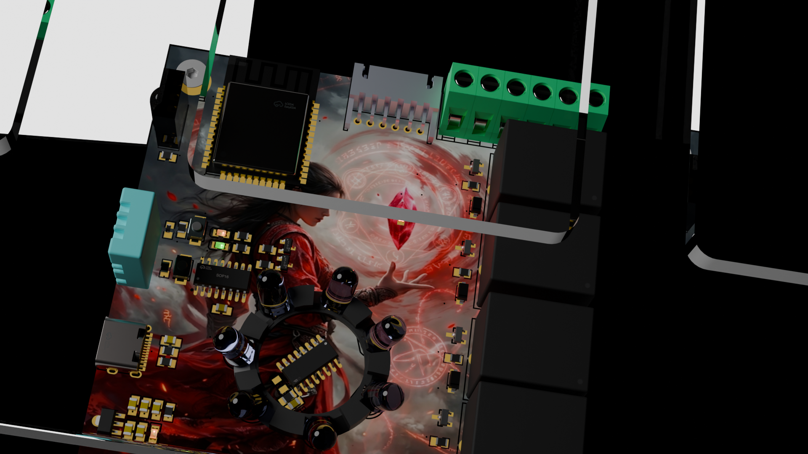
Render/ruby-render/0611.png
