dushyantyadav0303/Ruby-Home-Automation/Render/ruby-render/0612.png

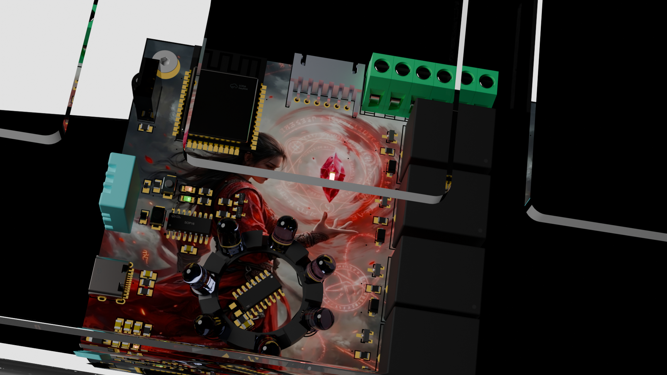
Render/ruby-render/0612.png
