dushyantyadav0303/Ruby-Home-Automation/Render/ruby-render/0616.png

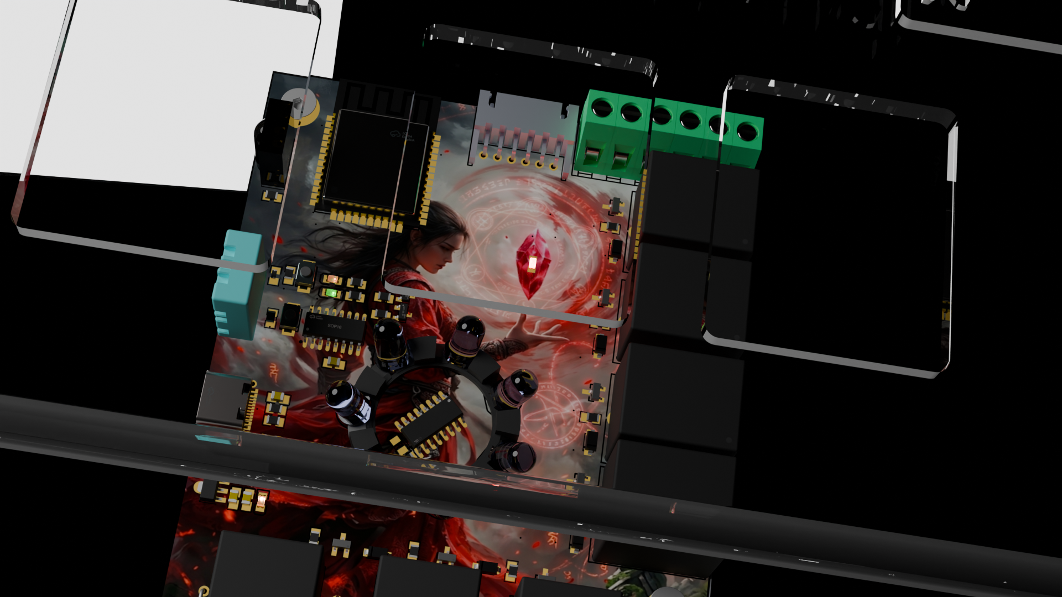
Render/ruby-render/0616.png
