dushyantyadav0303/Ruby-Home-Automation/Render/ruby-render/0618.png

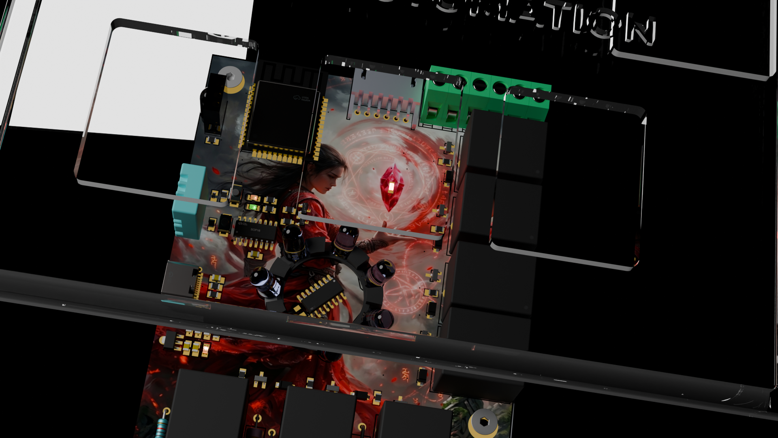
Render/ruby-render/0618.png
