dushyantyadav0303/Ruby-Home-Automation/Render/ruby-render/0619.png

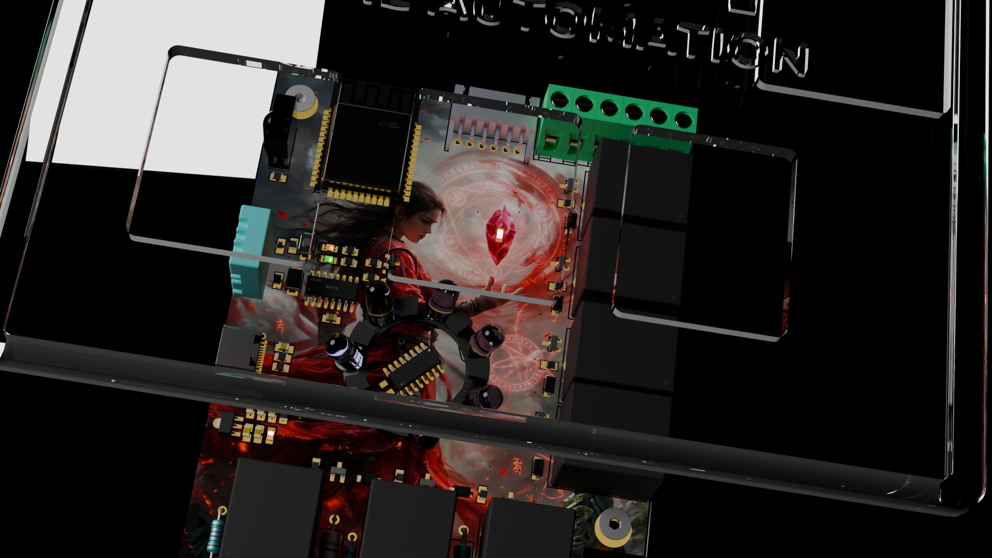
Render/ruby-render/0619.png
