dushyantyadav0303/Ruby-Home-Automation/Render/ruby-render/0621.png

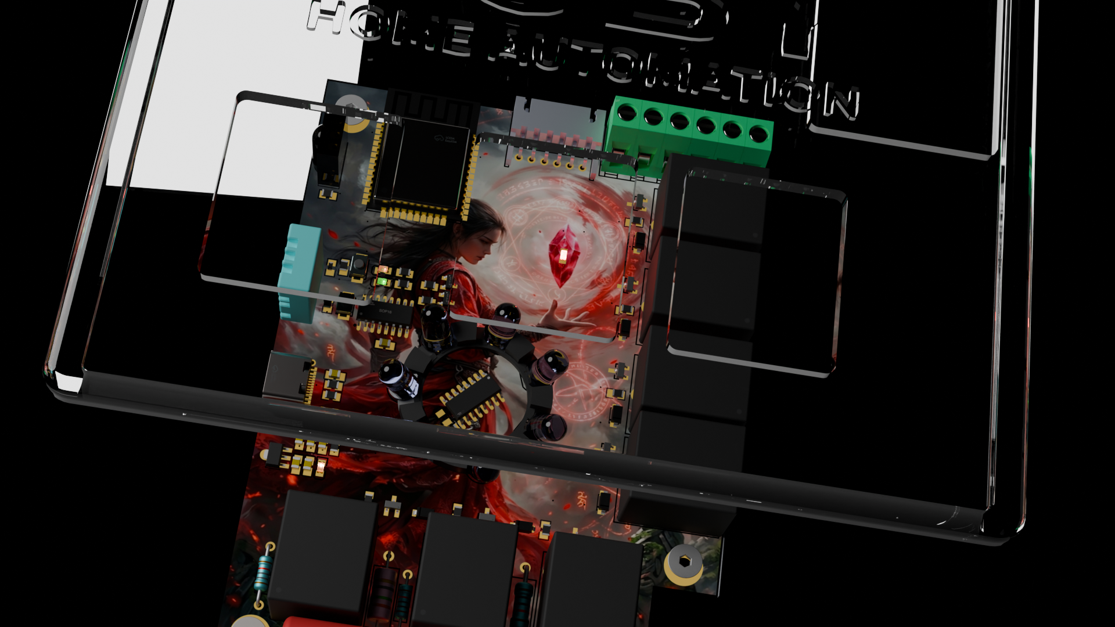
Render/ruby-render/0621.png
