dushyantyadav0303/Ruby-Home-Automation/Render/ruby-render/0623.png

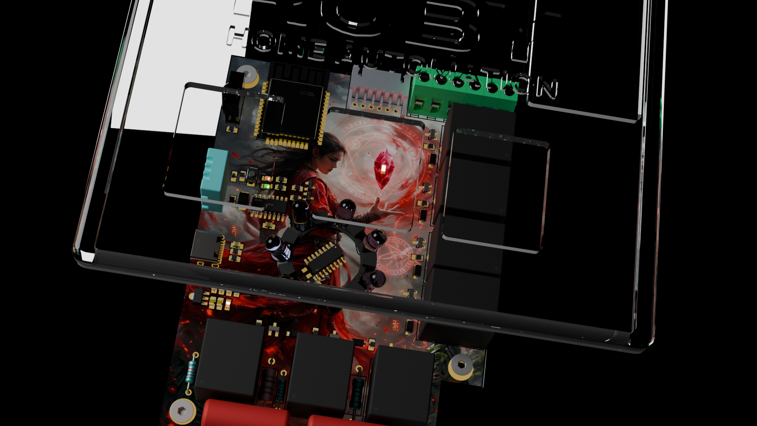
Render/ruby-render/0623.png
