dushyantyadav0303/Ruby-Home-Automation/Render/ruby-render/0627.png

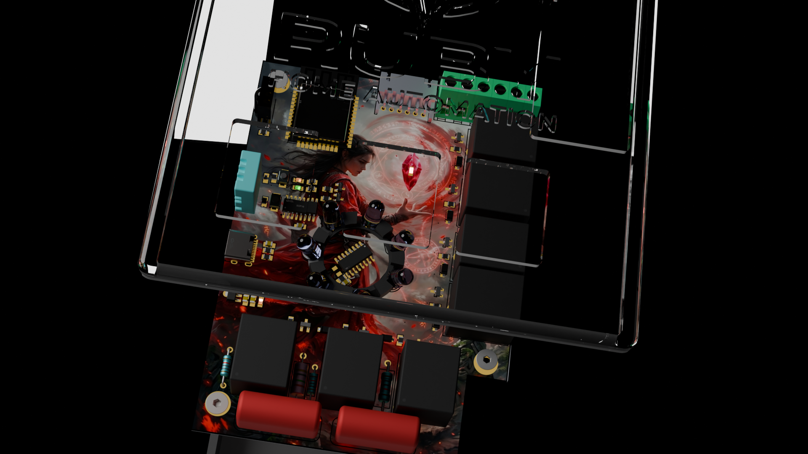
Render/ruby-render/0627.png
