dushyantyadav0303/Ruby-Home-Automation/Render/ruby-render/0630.png

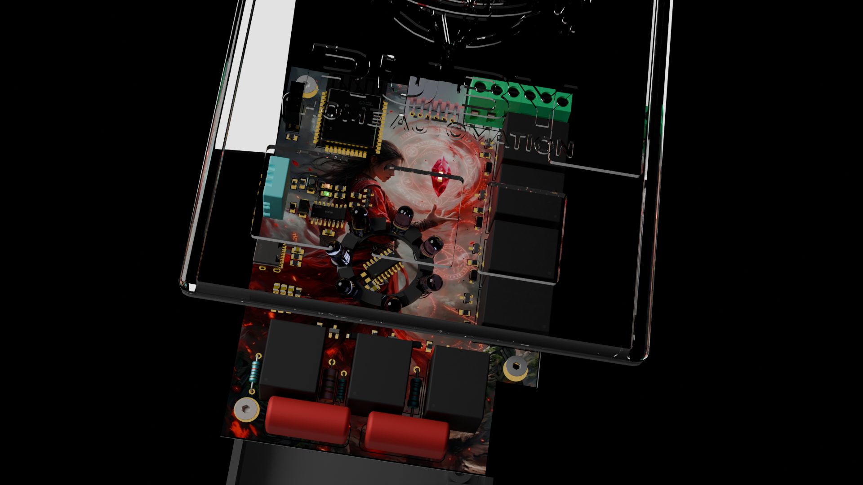
Render/ruby-render/0630.png
