dushyantyadav0303/Ruby-Home-Automation/Render/ruby-render/0642.png

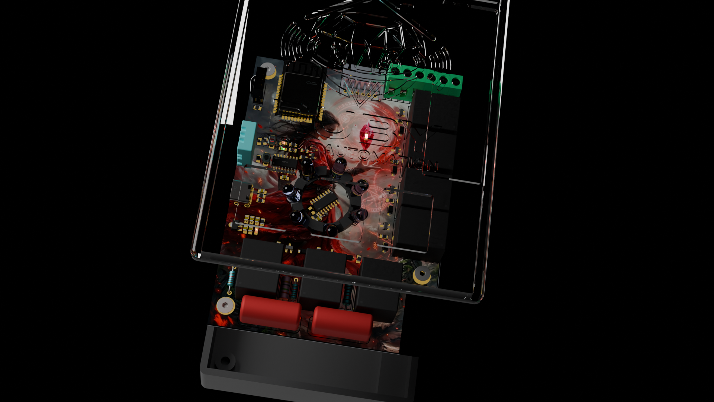
Render/ruby-render/0642.png
