dushyantyadav0303/Ruby-Home-Automation/Render/ruby-render/0651.png

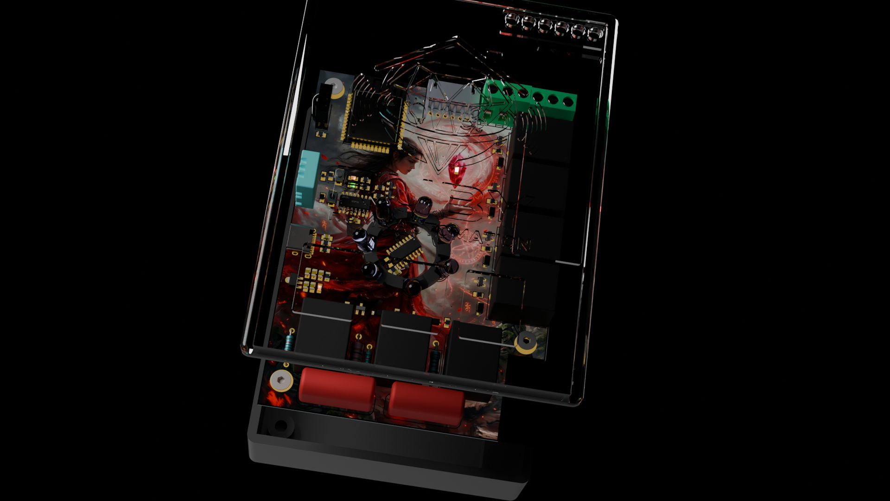
Render/ruby-render/0651.png
