dushyantyadav0303/Ruby-Home-Automation/Render/ruby-render/0664.png

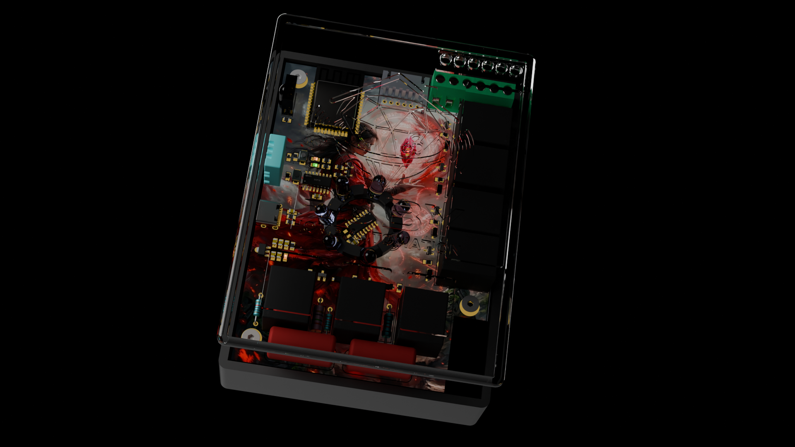
Render/ruby-render/0664.png
